dataders/adu_adoration/apartment/option-a-living-east.png

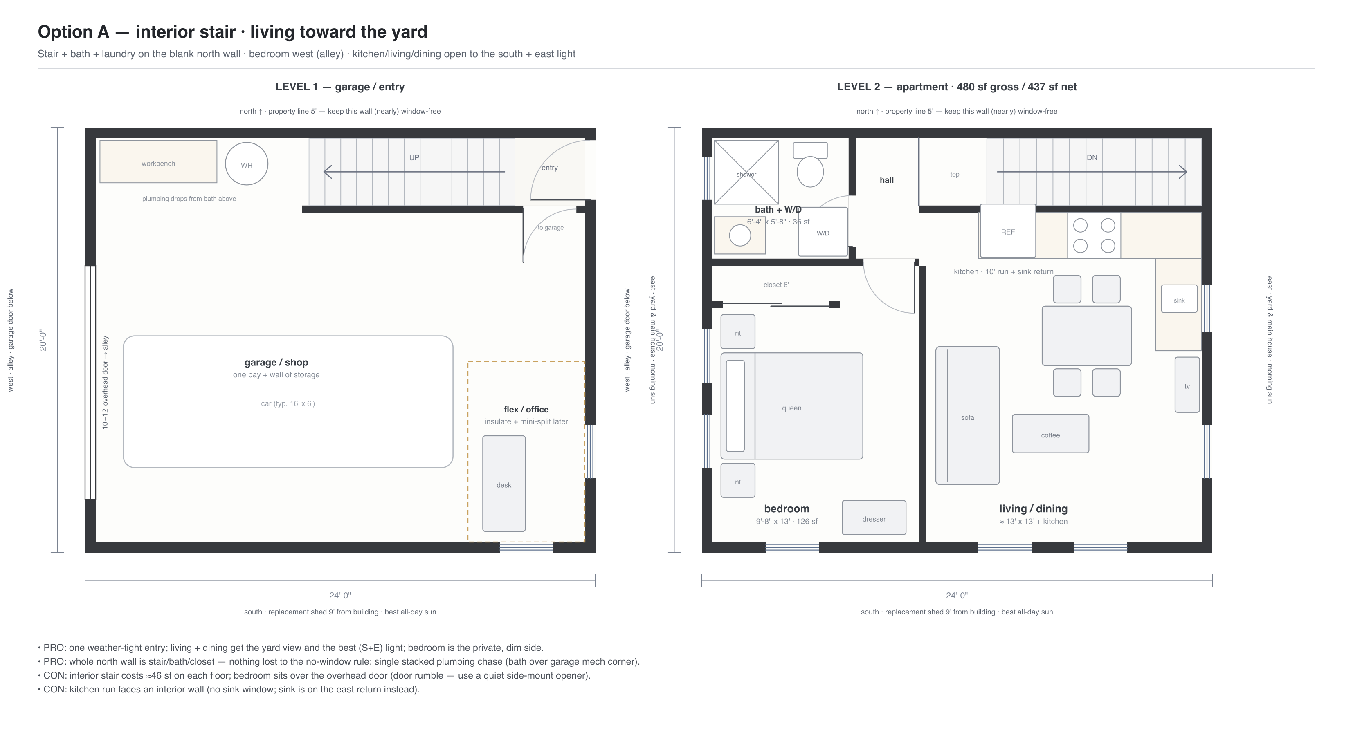
apartment/option-a-living-east.png
