dataders/adu_adoration/apartment/option-b-bedroom-east.png

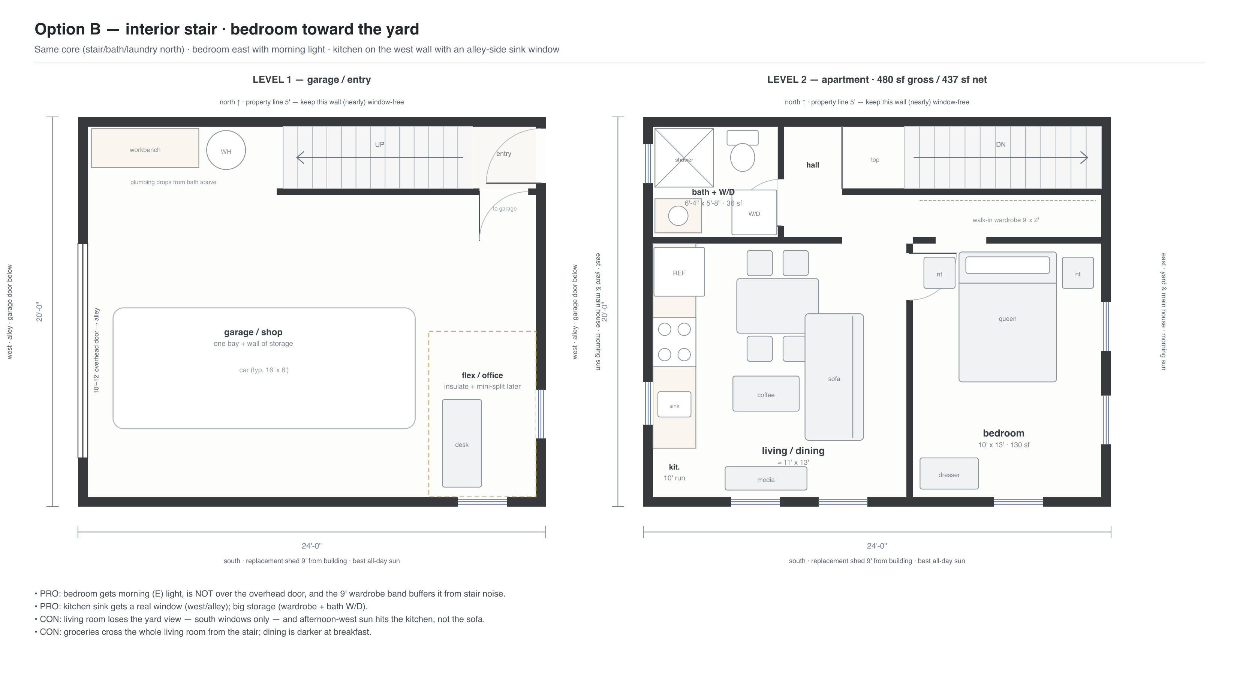
apartment/option-b-bedroom-east.png
