dataders/adu_adoration/apartment/option-c-exterior-stair.png

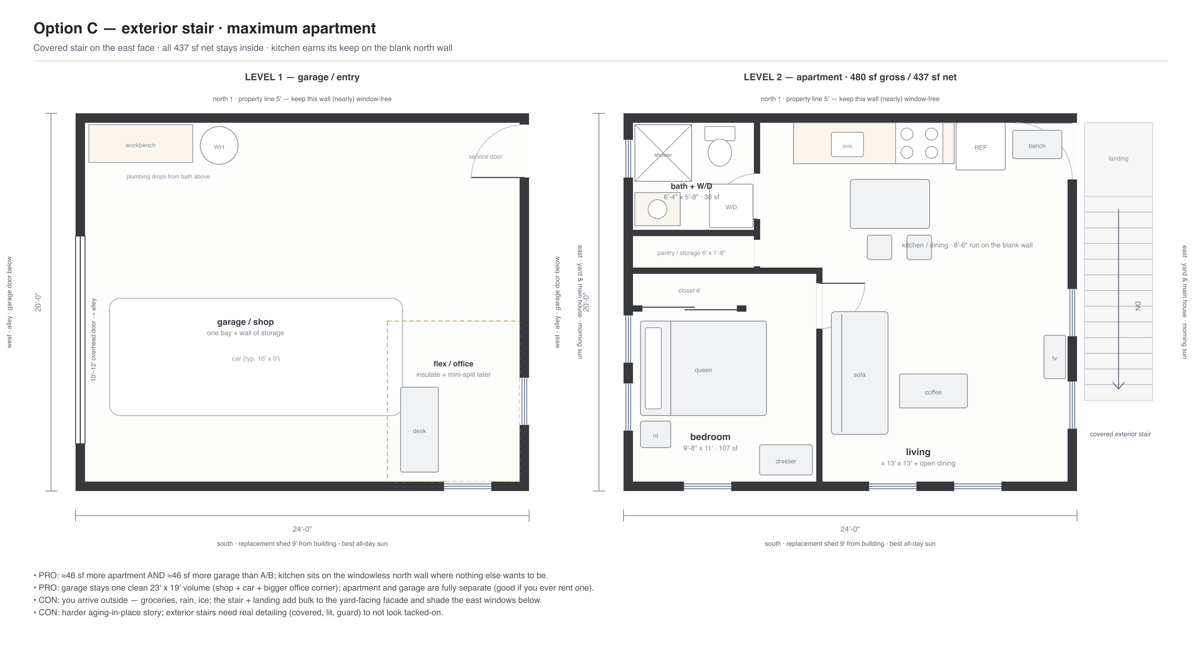
apartment/option-c-exterior-stair.png
