dataders/adu_adoration/apartment/option-d-south-stair-roof-aware.png

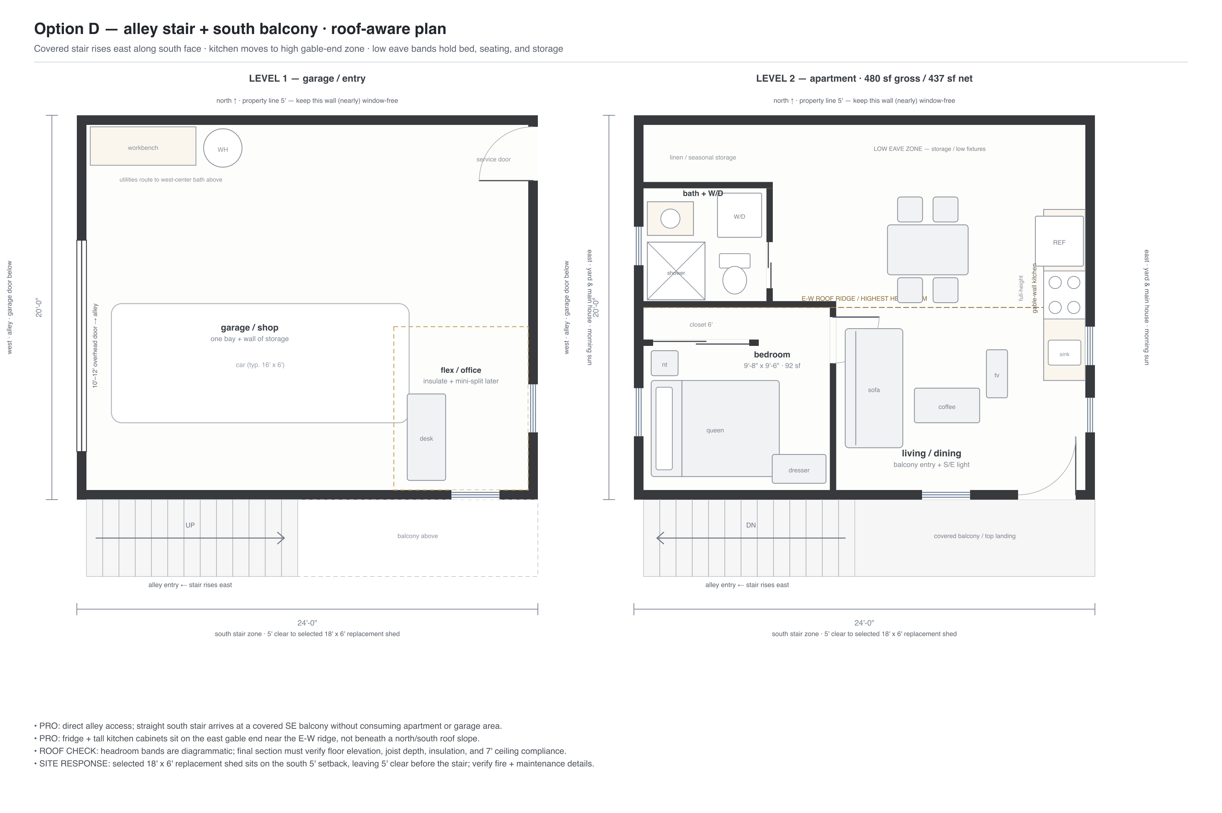
apartment/option-d-south-stair-roof-aware.png
