dataders/adu_adoration/apartment/option-f-alternative-garden.png

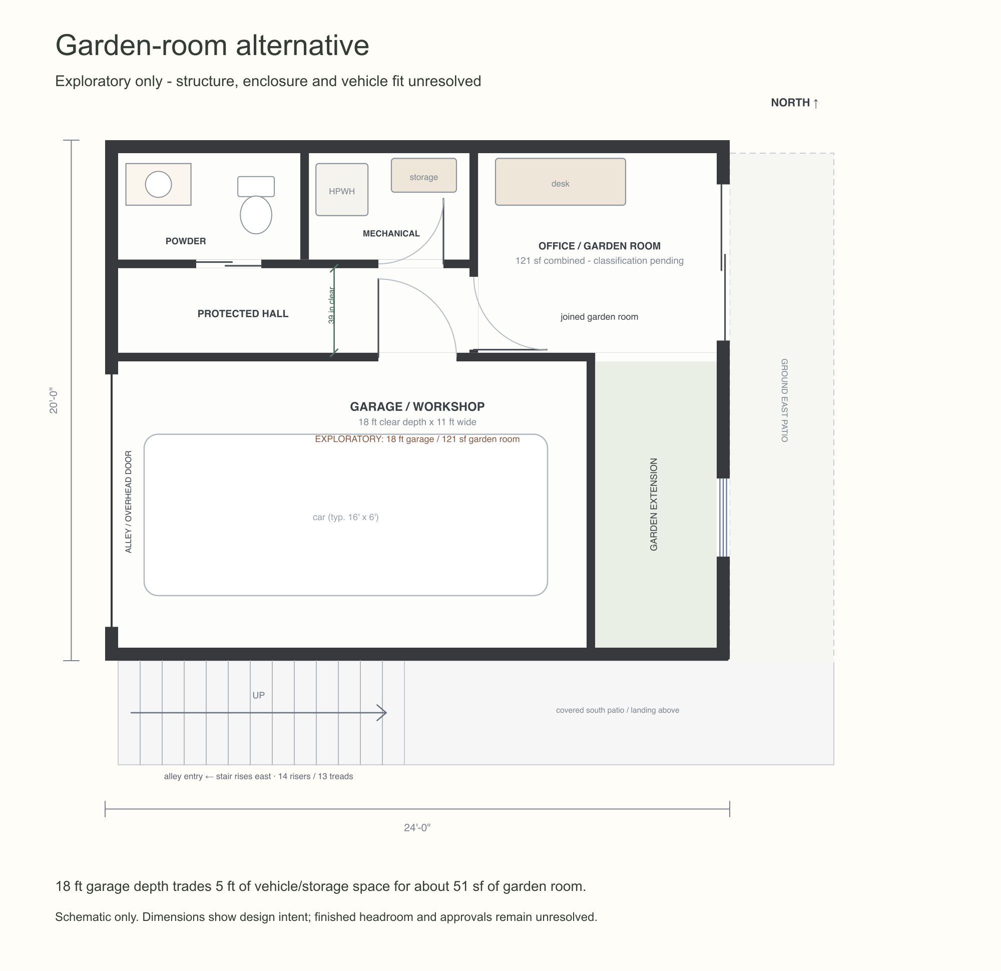
apartment/option-f-alternative-garden.png
