dataders/adu_adoration/apartment/option-f-level-1.png

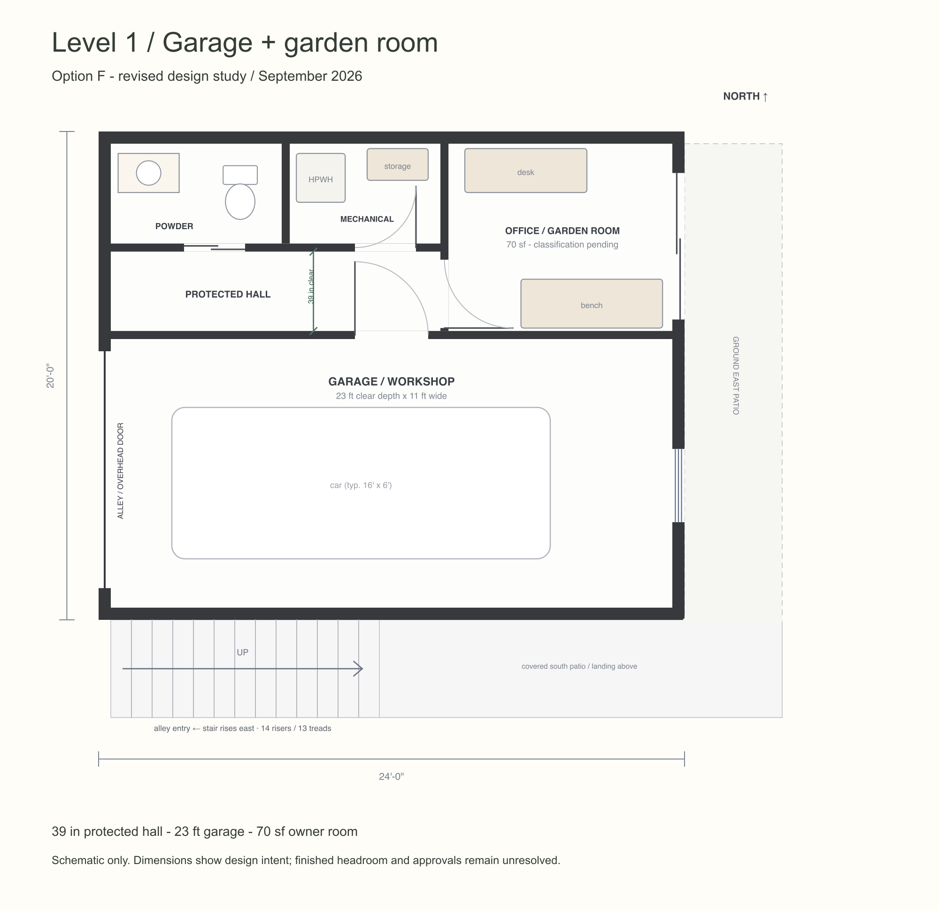
apartment/option-f-level-1.png
