dataders/adu_adoration/apartment/option-f-level-2.png

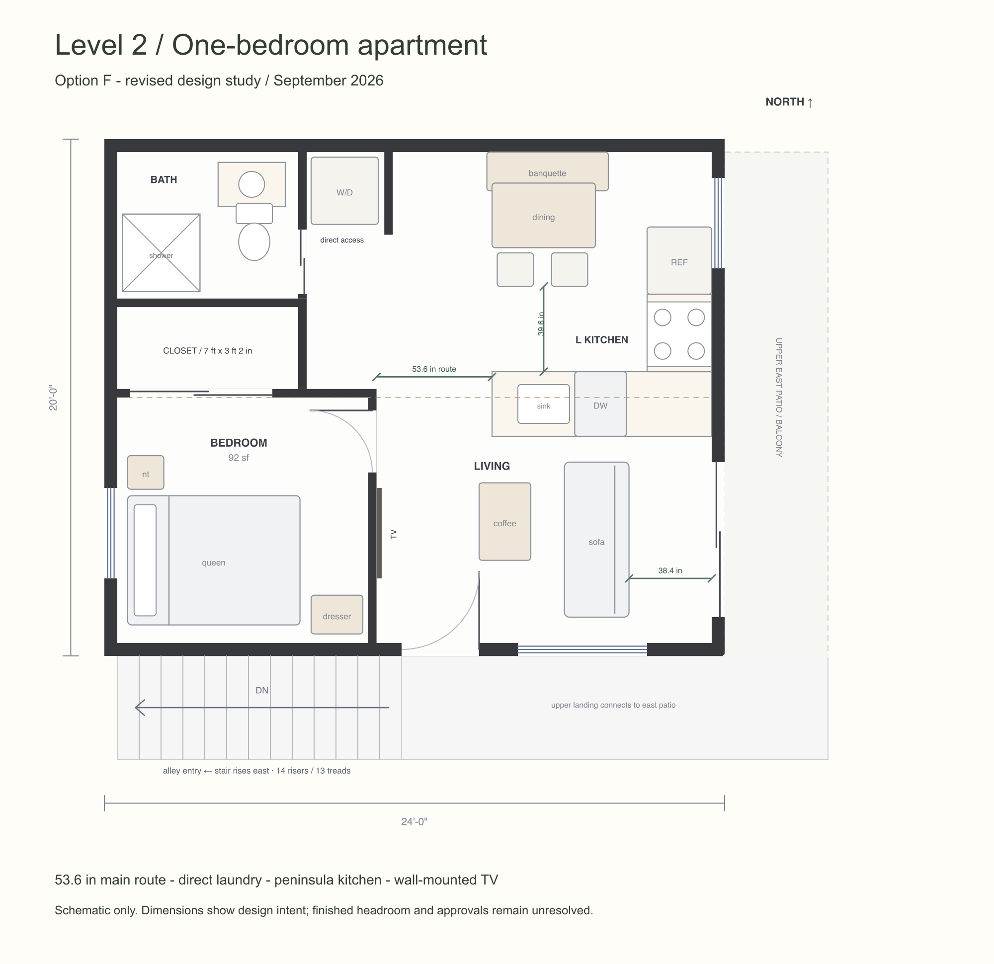
apartment/option-f-level-2.png
