dataders/adu_adoration/apartment/option-f-recommended-development.png

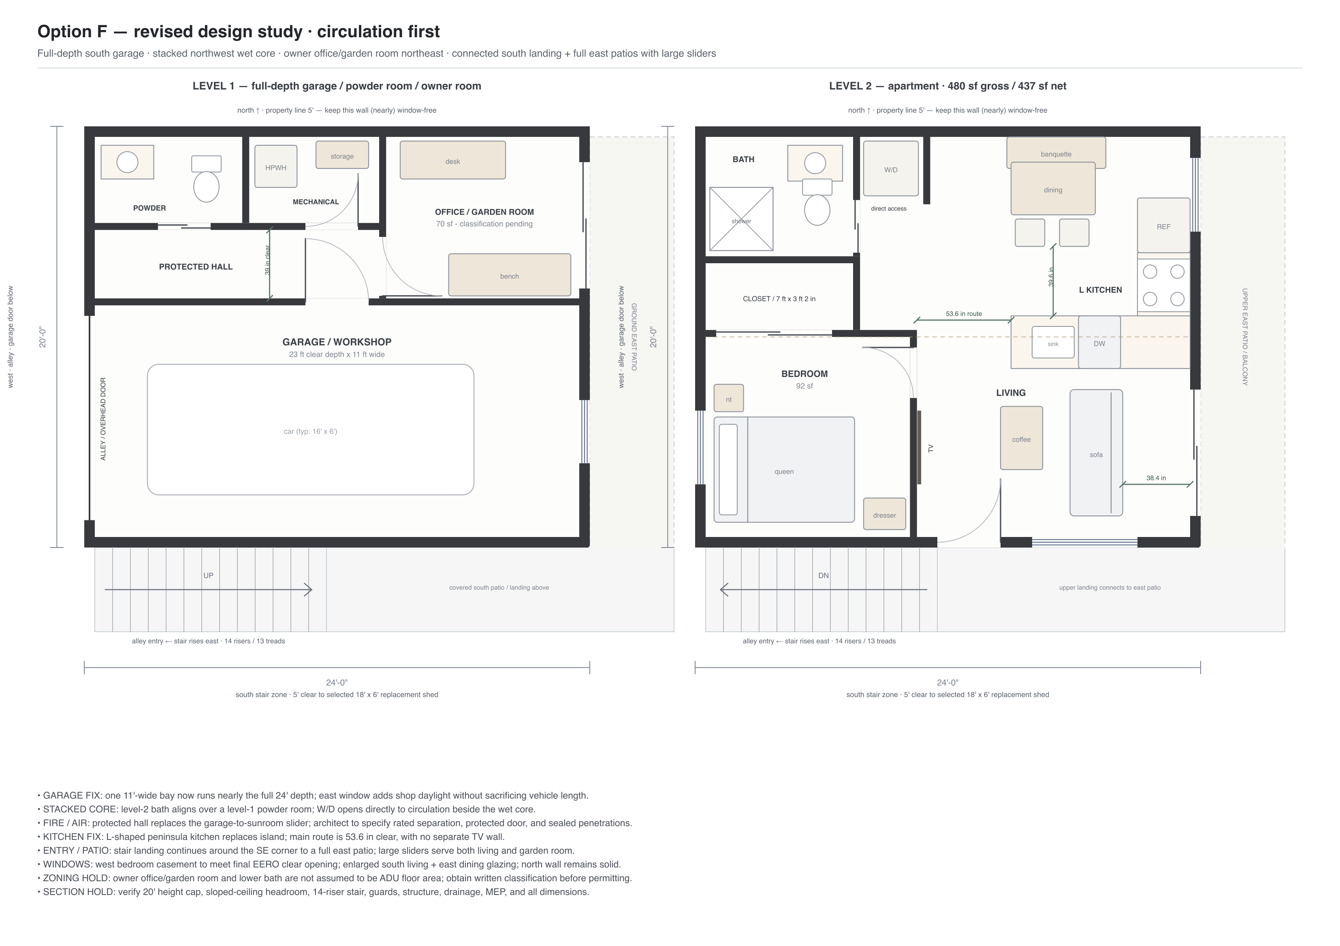
apartment/option-f-recommended-development.png
