dataders/adu_adoration/images/06-satellite-parcel-outline.png

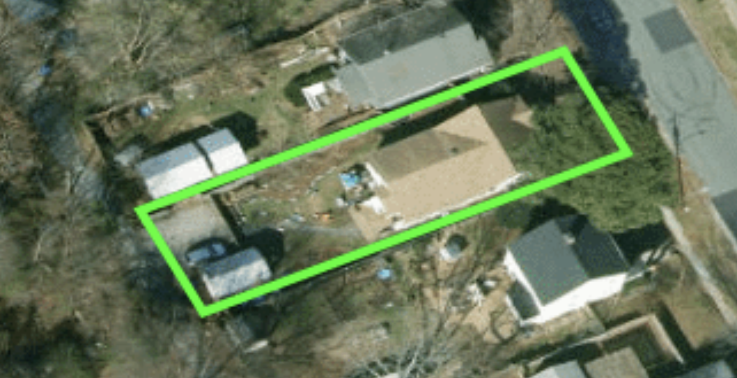
images/06-satellite-parcel-outline.png
