dataders/adu_adoration/images/07-satellite-oblique-3d.png

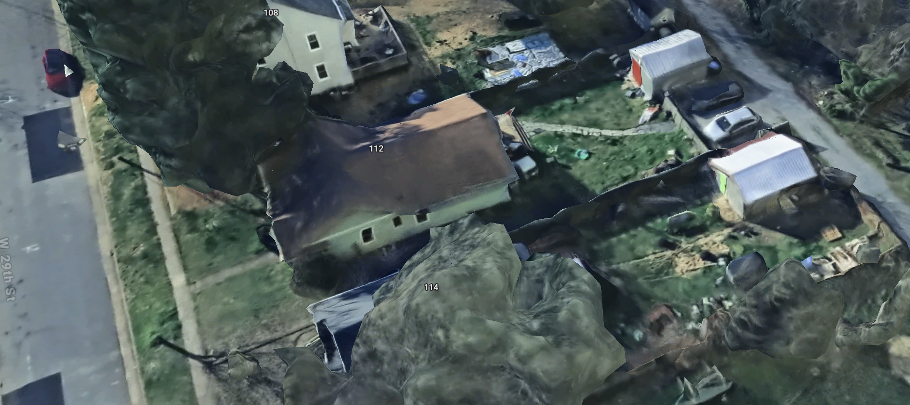
images/07-satellite-oblique-3d.png
