dataders/adu_adoration/images/09-backyard-shed-facing-west.jpg

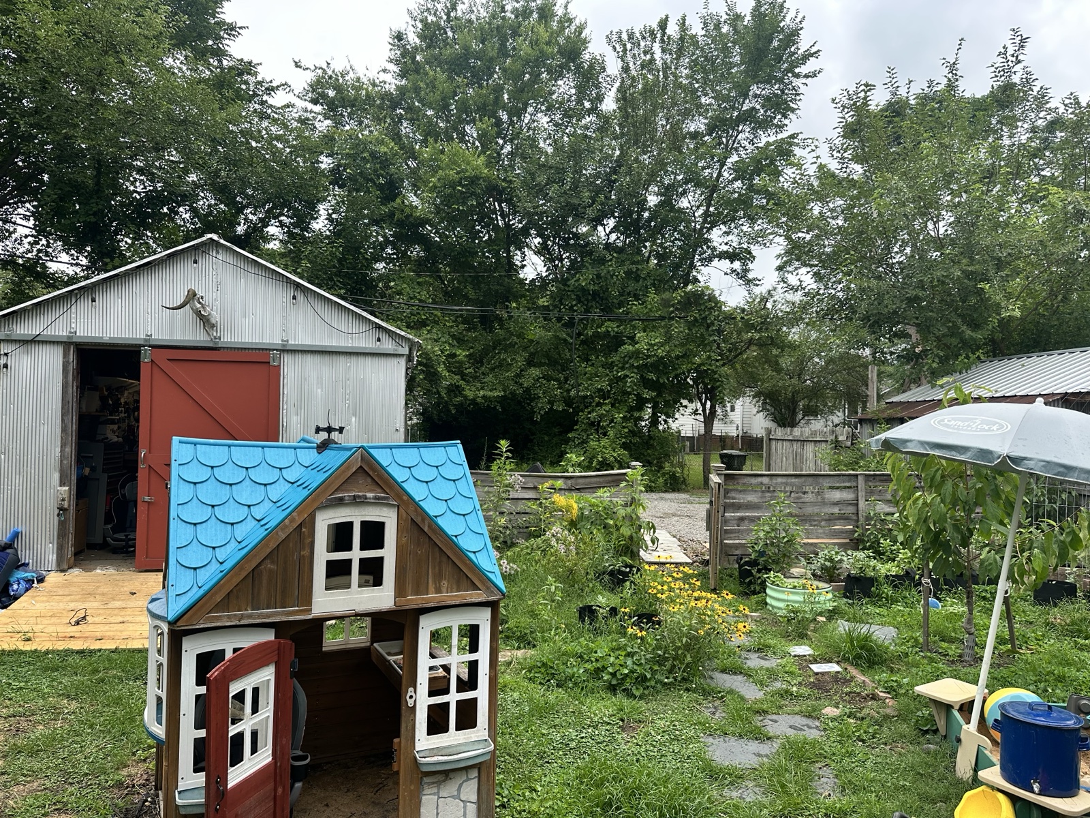
images/09-backyard-shed-facing-west.jpg
