dataders/adu_adoration/images/11-backyard-alley-parking-facing-east.jpg

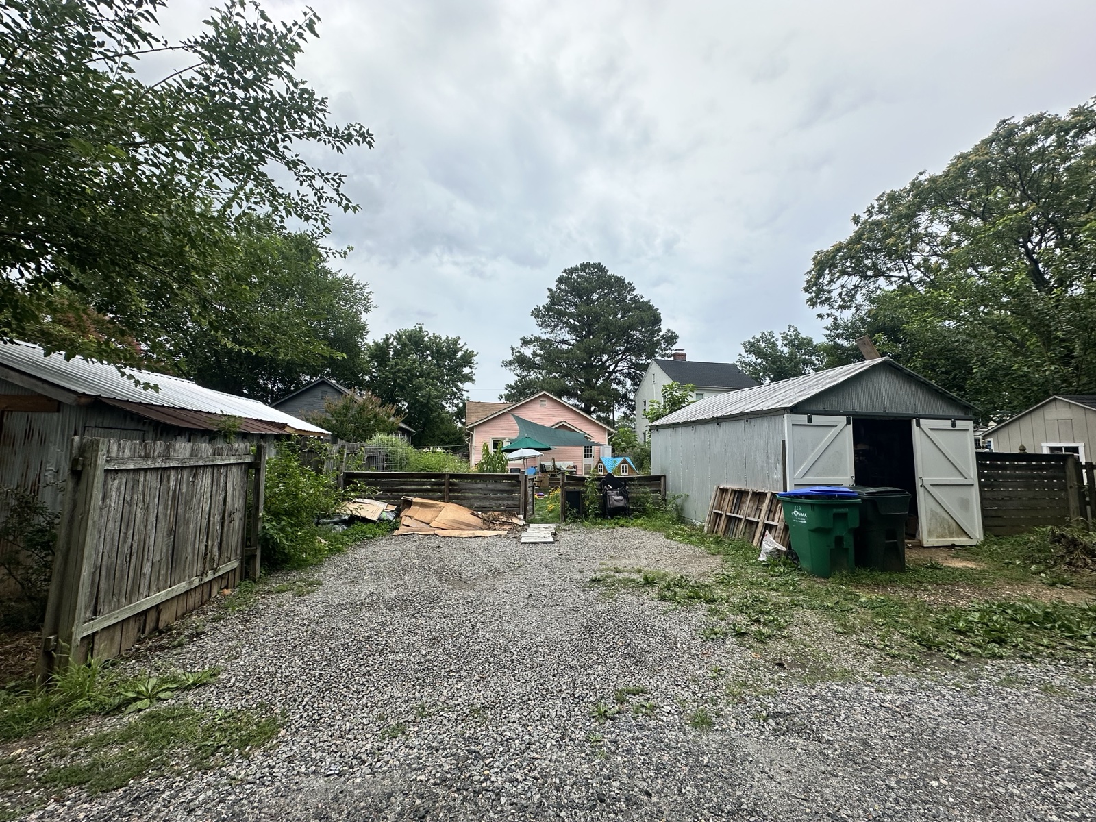
images/11-backyard-alley-parking-facing-east.jpg
