dataders/adu_adoration/inspiration/01-gold-siding-black-windows-bay-tower.jpg

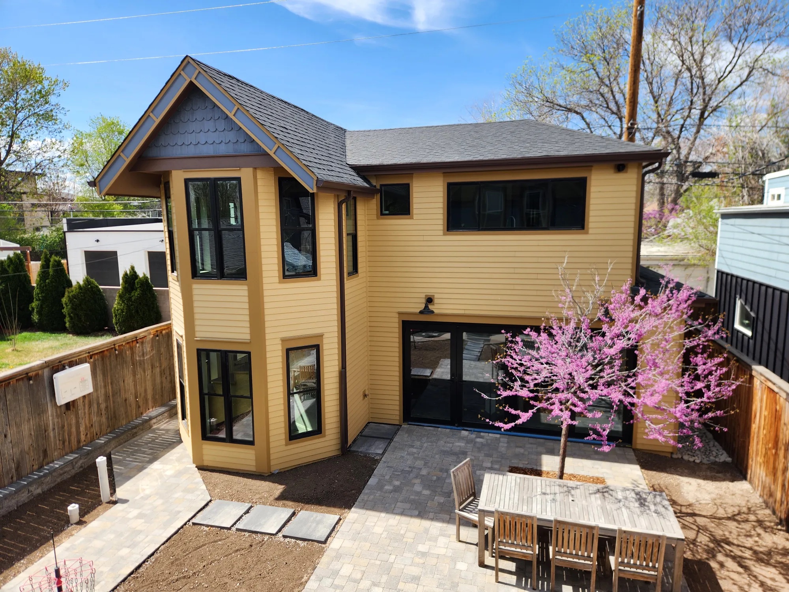
inspiration/01-gold-siding-black-windows-bay-tower.jpg
