dataders/adu_adoration/inspiration/02-modern-taupe-shed-roof-awning-windows.jpg

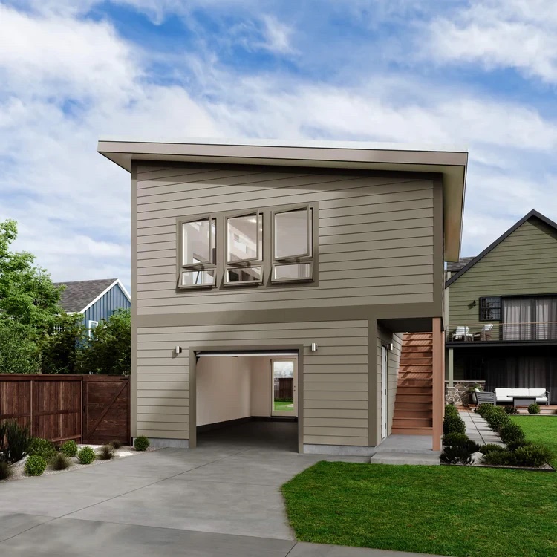
inspiration/02-modern-taupe-shed-roof-awning-windows.jpg
