dataders/adu_adoration/inspiration/03-craftsman-gray-red-trim-carriage-door.jpg

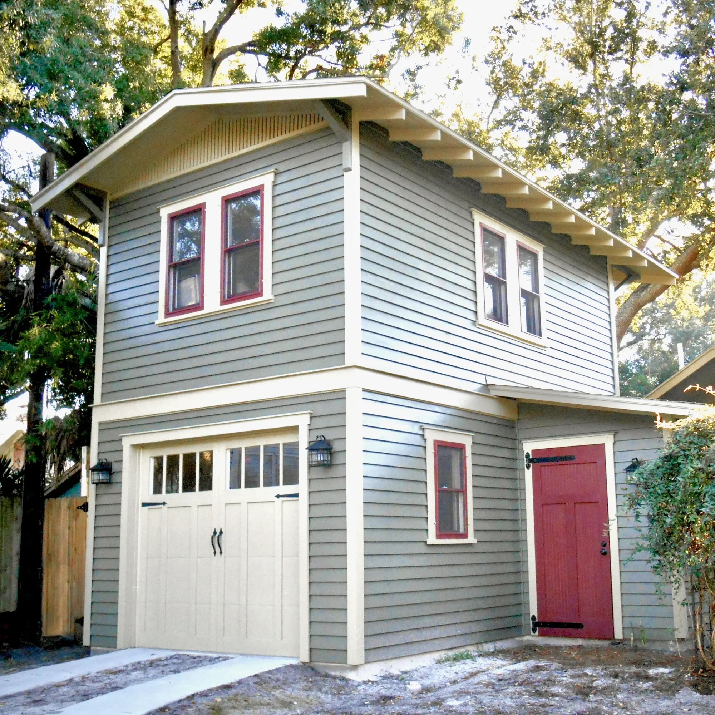
inspiration/03-craftsman-gray-red-trim-carriage-door.jpg
