dataders/adu_adoration/inspiration/04-olive-carriage-door-balcony-cottage.jpg

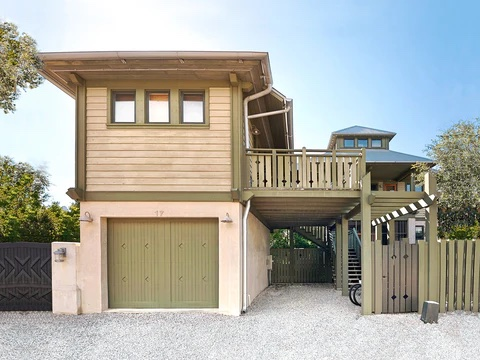
inspiration/04-olive-carriage-door-balcony-cottage.jpg
