dataders/adu_adoration/inspiration/05-brick-shed-roof-black-windows-wood-door.jpg

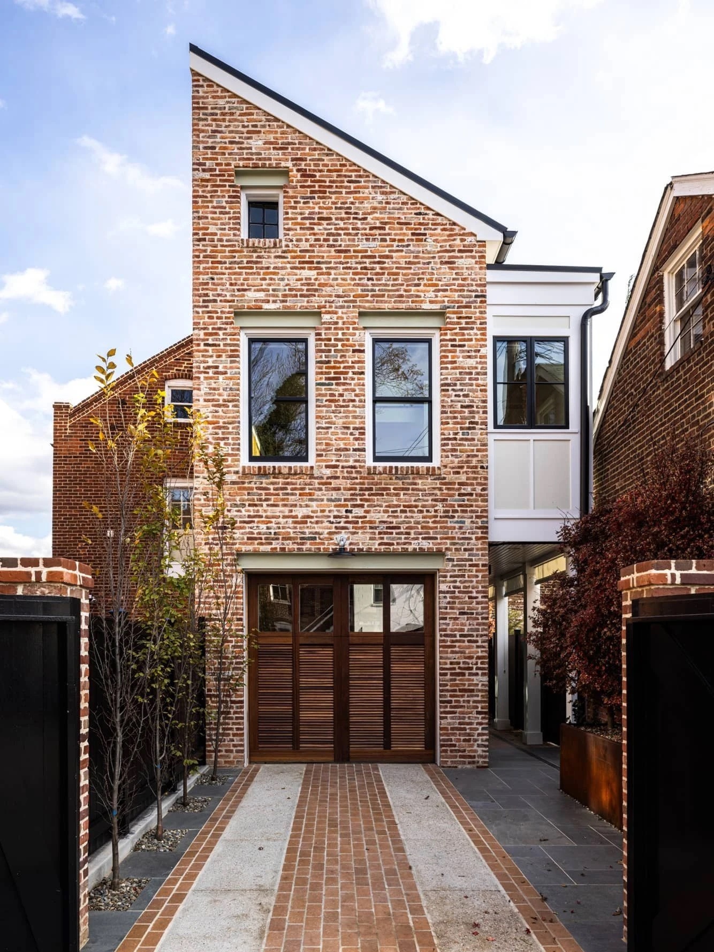
inspiration/05-brick-shed-roof-black-windows-wood-door.jpg
