dataders/adu_adoration/inspiration/06-modern-olive-bronze-windows-corner-glass.jpg

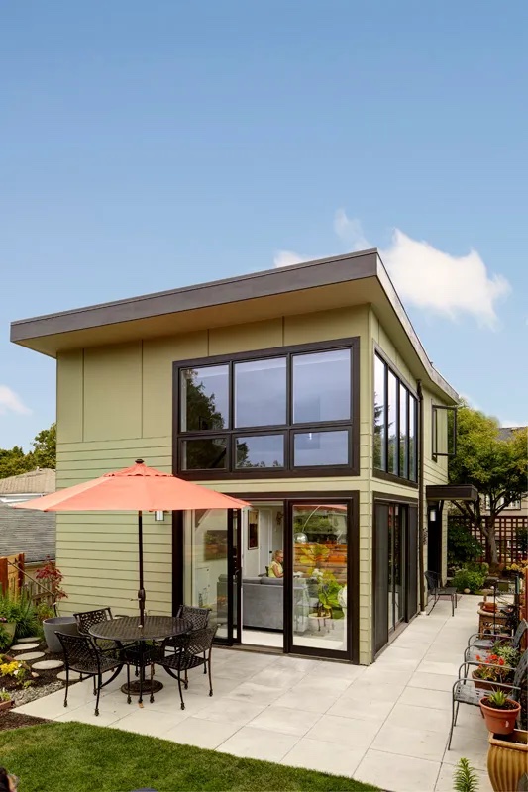
inspiration/06-modern-olive-bronze-windows-corner-glass.jpg
