dataders/adu_adoration/inspiration/pin-407012885098091217-pin.jpg

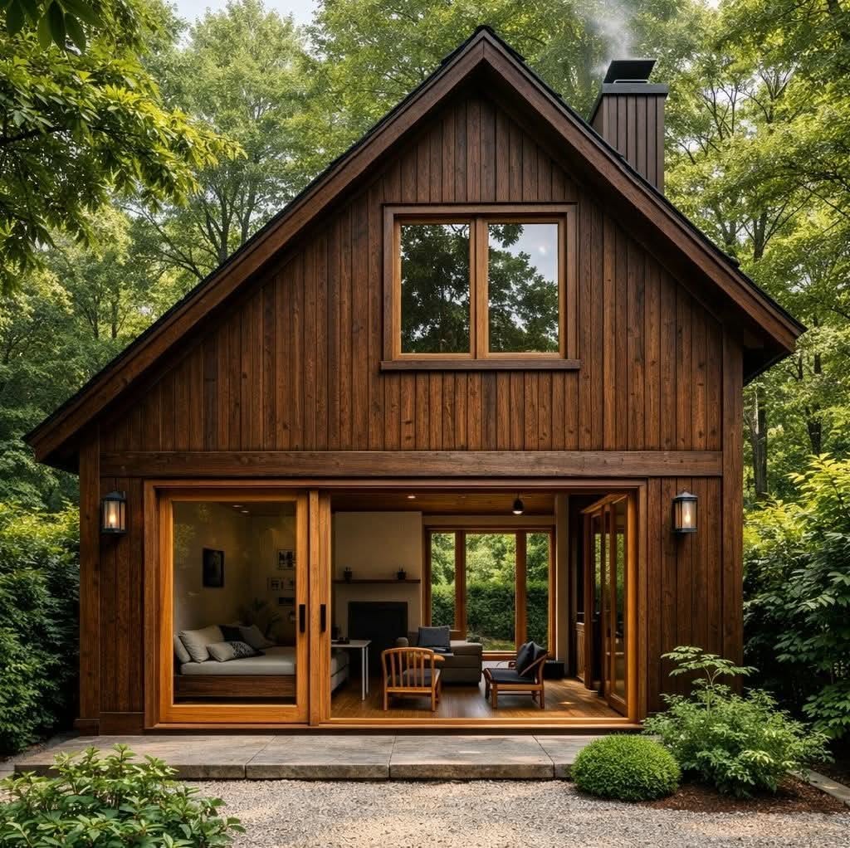
inspiration/pin-407012885098091217-pin.jpg
