dataders/adu_adoration/inspiration/pin-407012885098092414-62k-views-1-4k-reactions-a-small-cabin-a-big-for.jpg

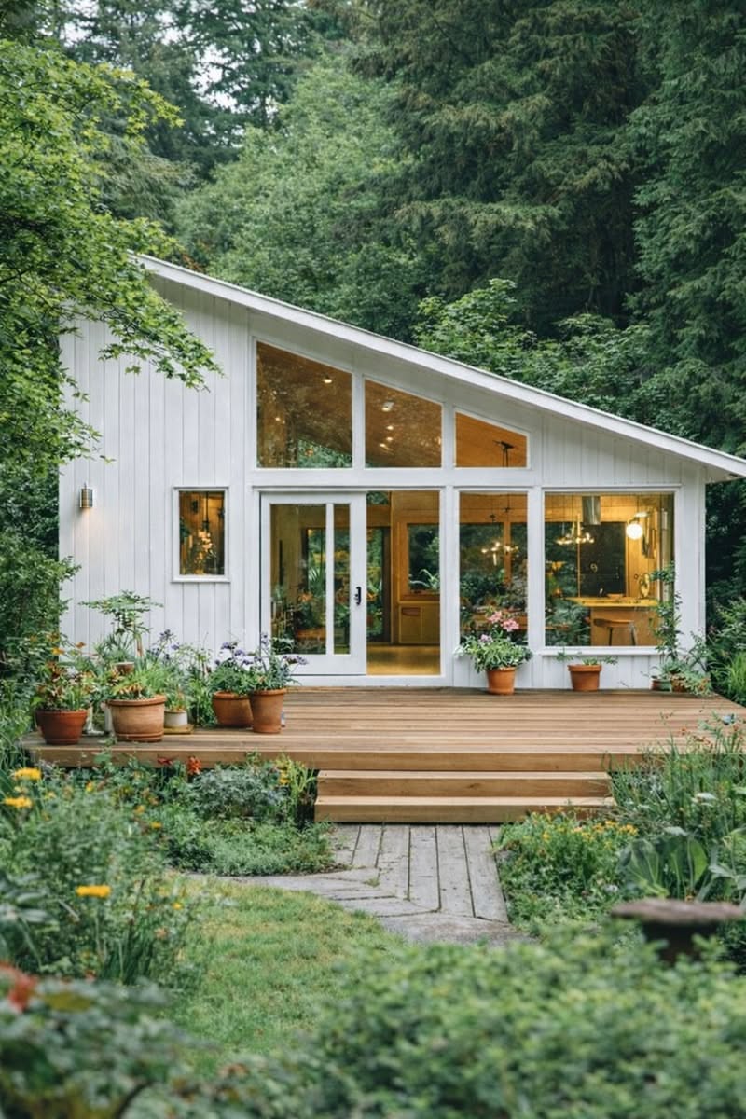
inspiration/pin-407012885098092414-62k-views-1-4k-reactions-a-small-cabin-a-big-for.jpg
