dataders/adu_adoration/inspiration/pin-407012885098092424-green-craftsman-shed-with-wooden-doors-and-bear.jpg

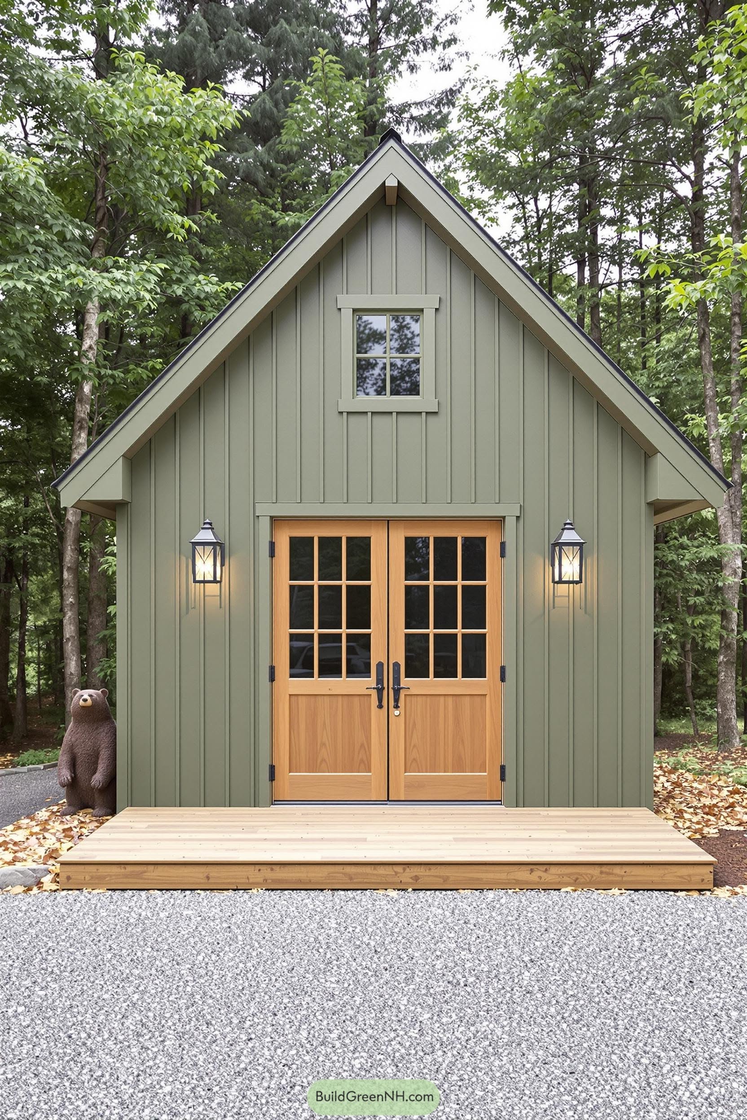
inspiration/pin-407012885098092424-green-craftsman-shed-with-wooden-doors-and-bear.jpg
