dataders/adu_adoration/inspiration/pin-407012885098092436-the-apartment-above-the-garage-received-a-dormer.jpg

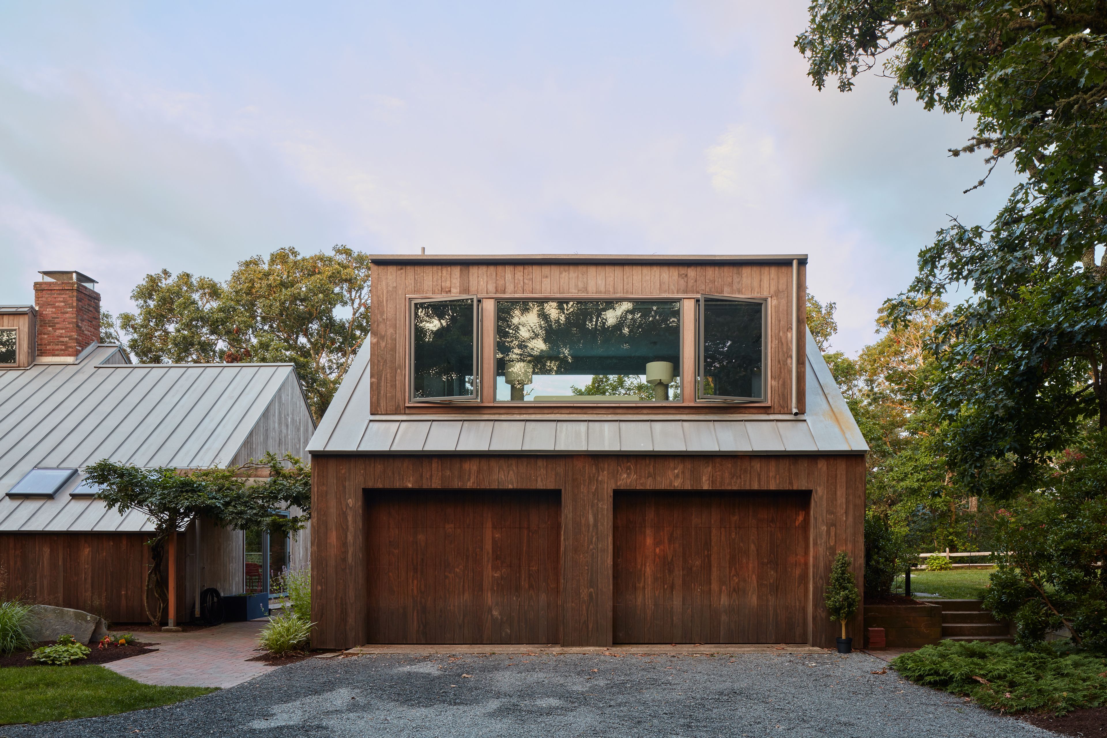
inspiration/pin-407012885098092436-the-apartment-above-the-garage-received-a-dormer.jpg
