dataders/adu_adoration/inspiration/pin-407012885098092439-a-brunswick-home-re-beautified-decor-maine.jpg

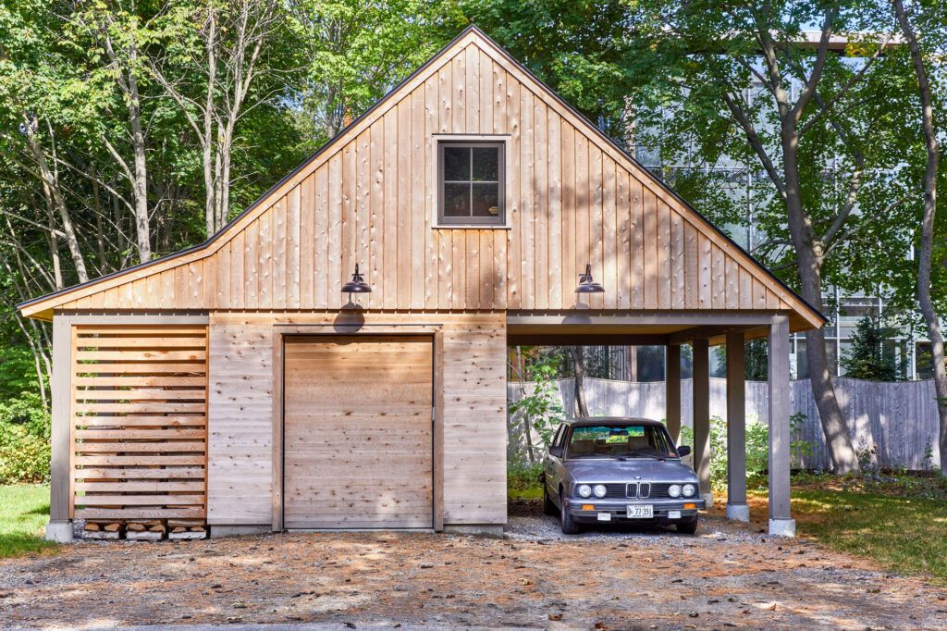
inspiration/pin-407012885098092439-a-brunswick-home-re-beautified-decor-maine.jpg
