dataders/adu_adoration/inspiration/pin-407012885098092445-pin.jpg

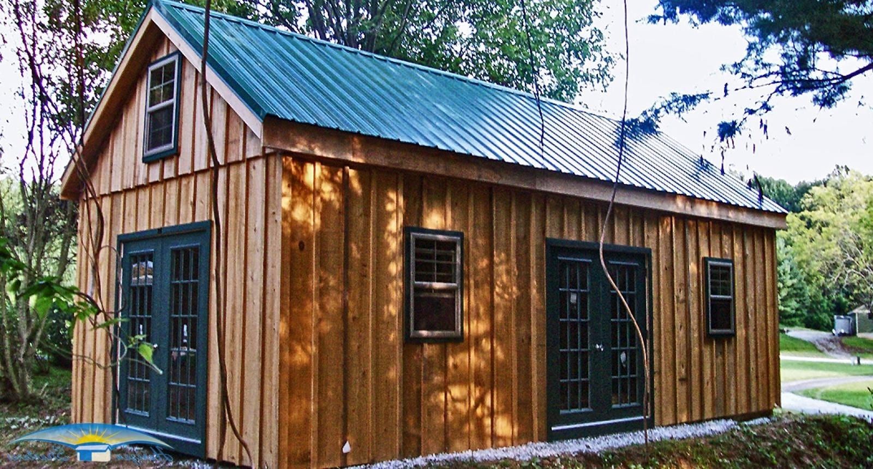
inspiration/pin-407012885098092445-pin.jpg
