dataders/adu_adoration/inspiration/pin-407012885098092450-pin.jpg

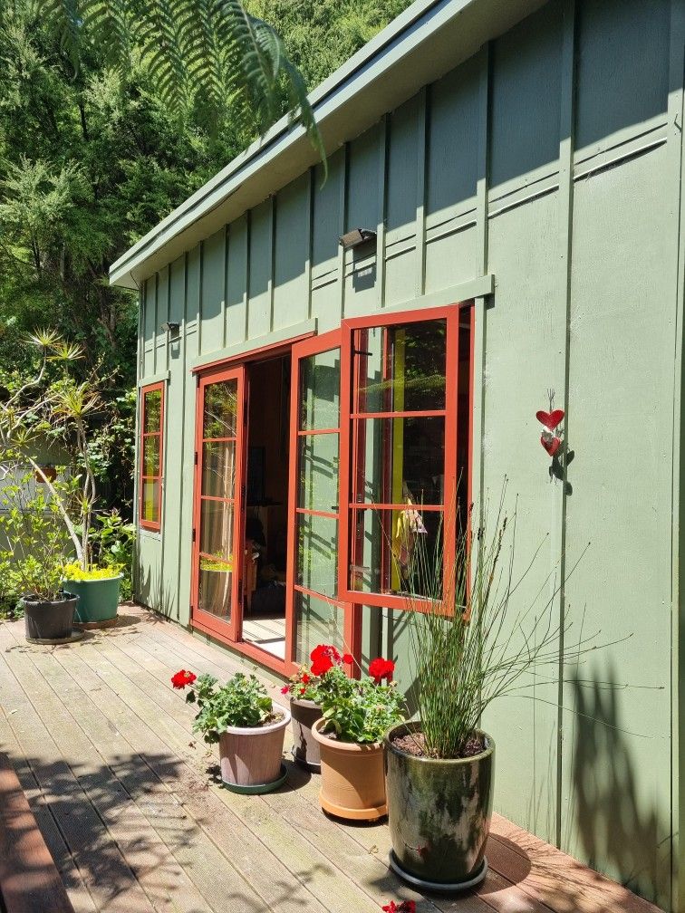
inspiration/pin-407012885098092450-pin.jpg
