dataders/adu_adoration/inspiration/pin-407012885098092619-experience-the-meticulous-craftsmanship-of-our-c.jpg

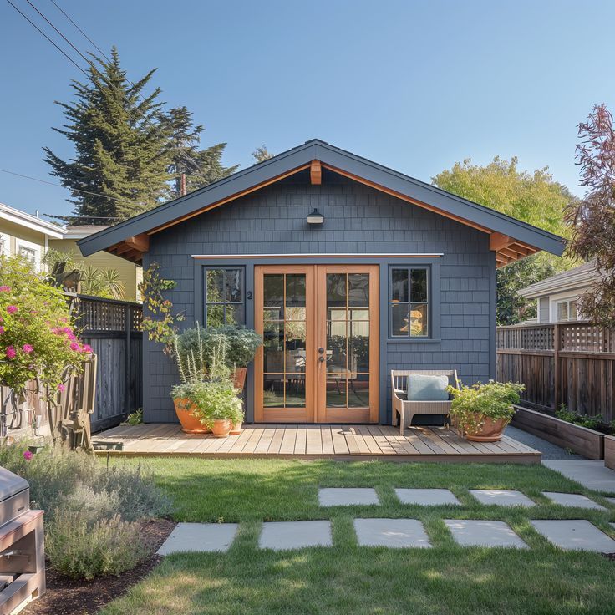
inspiration/pin-407012885098092619-experience-the-meticulous-craftsmanship-of-our-c.jpg
