dataders/adu_adoration/inspiration/pin-407012885098092621-rent-out-your-large-family-home-and-live-in-an-a.jpg

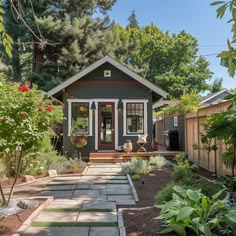
inspiration/pin-407012885098092621-rent-out-your-large-family-home-and-live-in-an-a.jpg
