dataders/adu_adoration/inspiration/pin-407012885098092629-15.jpg

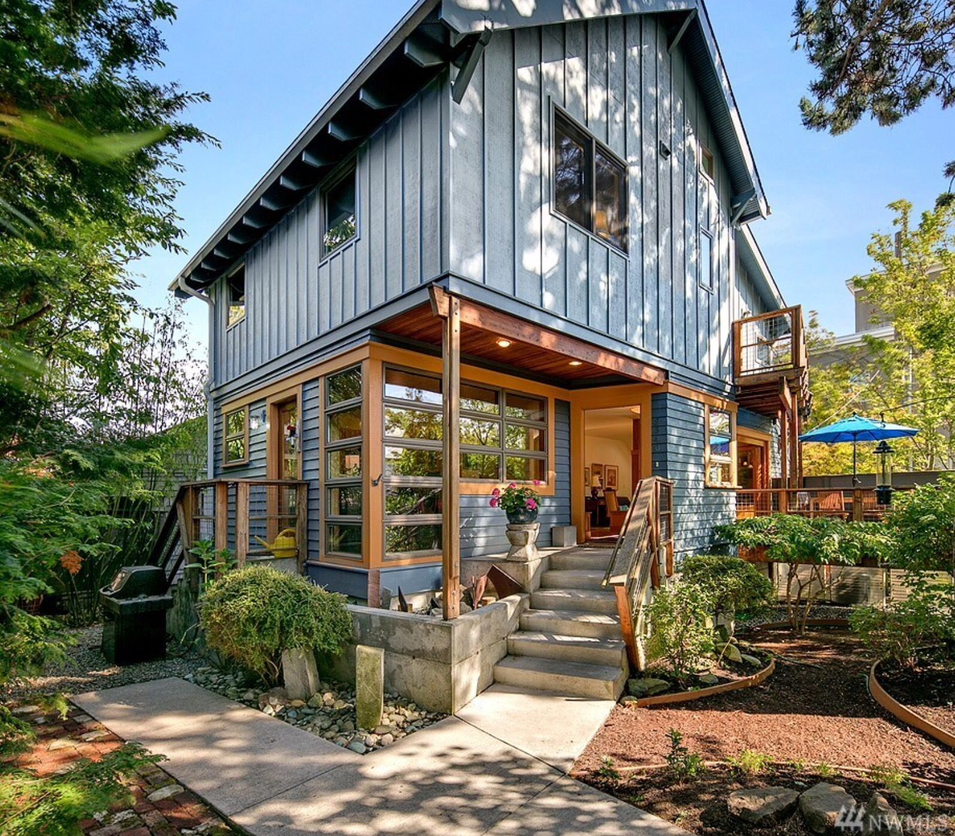
inspiration/pin-407012885098092629-15.jpg
