dataders/adu_adoration/inspiration/pin-407012885098092632-garden-garage-apartment-with-glass-corner-sunroo.jpg

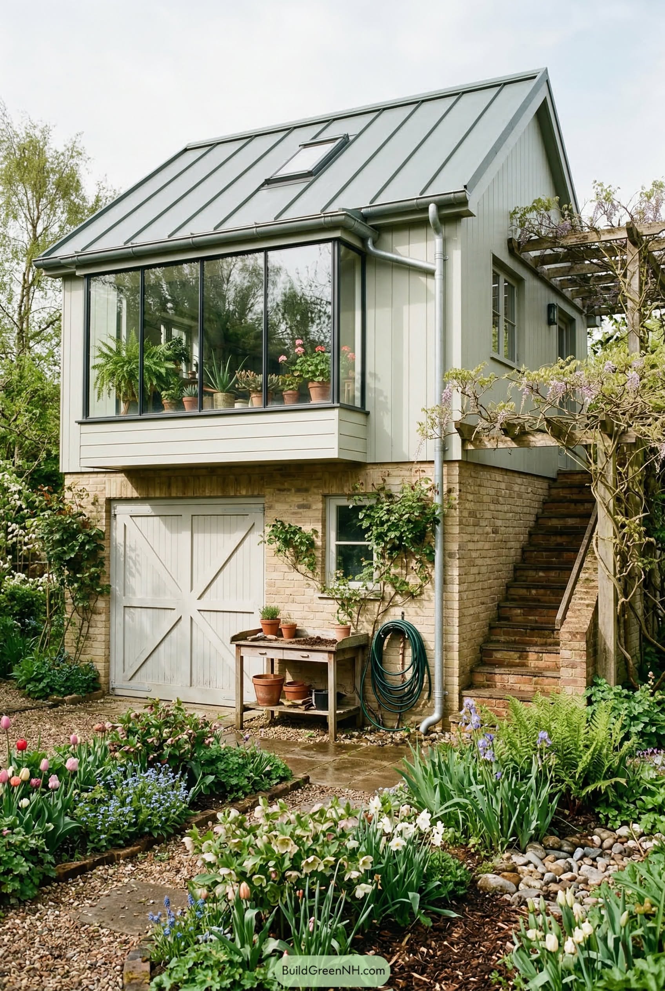
inspiration/pin-407012885098092632-garden-garage-apartment-with-glass-corner-sunroo.jpg
