dataders/adu_adoration/inspiration/pin-407012885098092633-blue-gray-two-story-garage-apartment-in-lush-gar.jpg

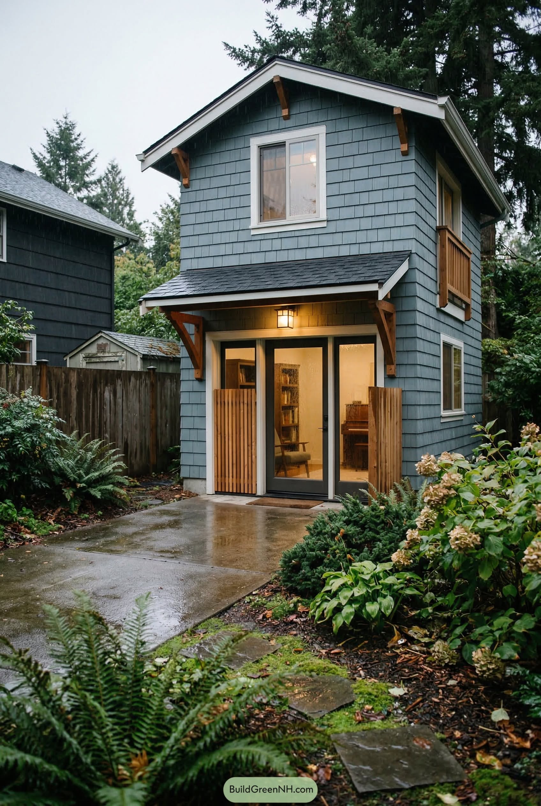
inspiration/pin-407012885098092633-blue-gray-two-story-garage-apartment-in-lush-gar.jpg
