dataders/adu_adoration/inspiration/pin-407012885098095681-pin.jpg

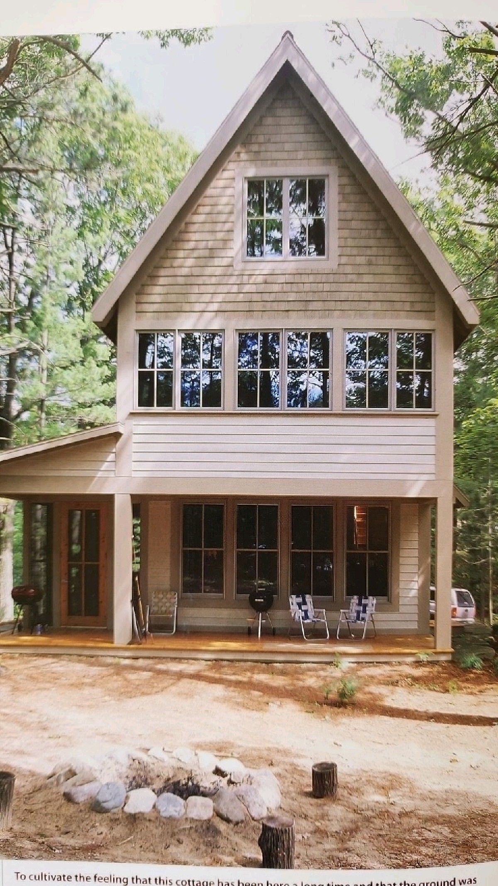
inspiration/pin-407012885098095681-pin.jpg
