dataders/adu_adoration/inspiration/pin-407012885098095682-pin.jpg

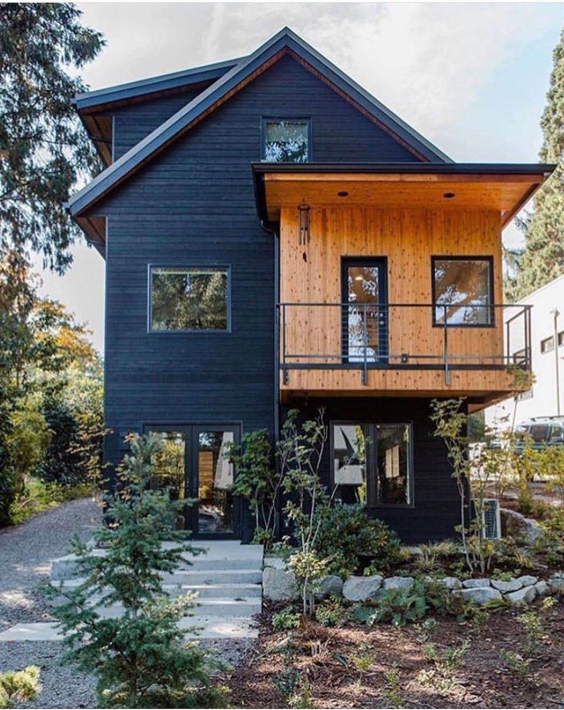
inspiration/pin-407012885098095682-pin.jpg
