dataders/adu_adoration/model/adu-option-e-axon.png

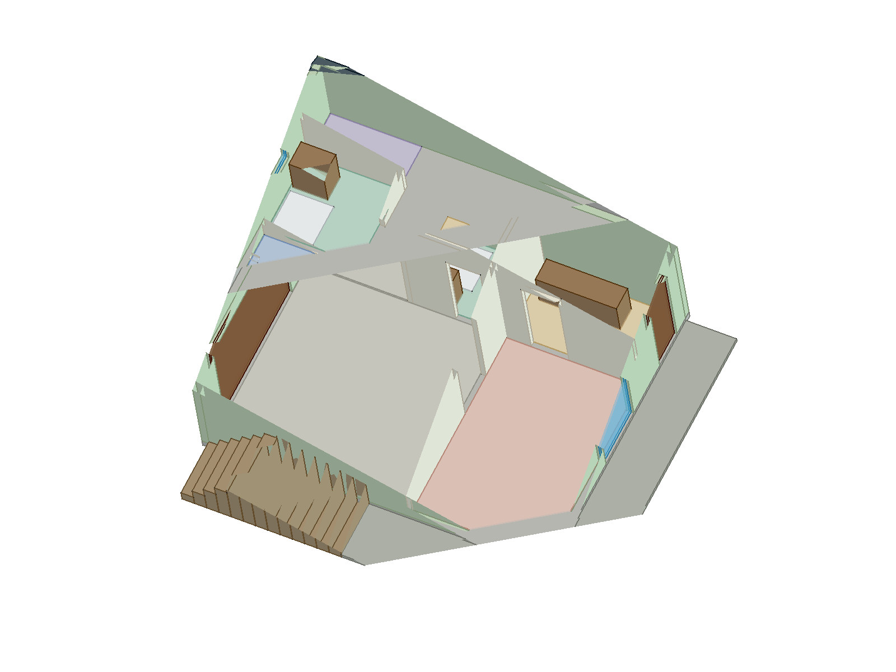
model/adu-option-e-axon.png
