dataders/adu_adoration/model/adu-option-e-level-1.png

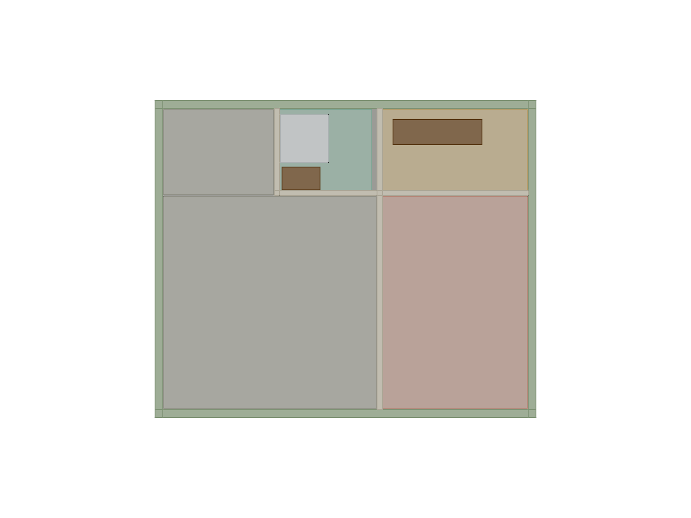
model/adu-option-e-level-1.png
