dataders/adu_adoration/model/adu-option-e-level-2.png

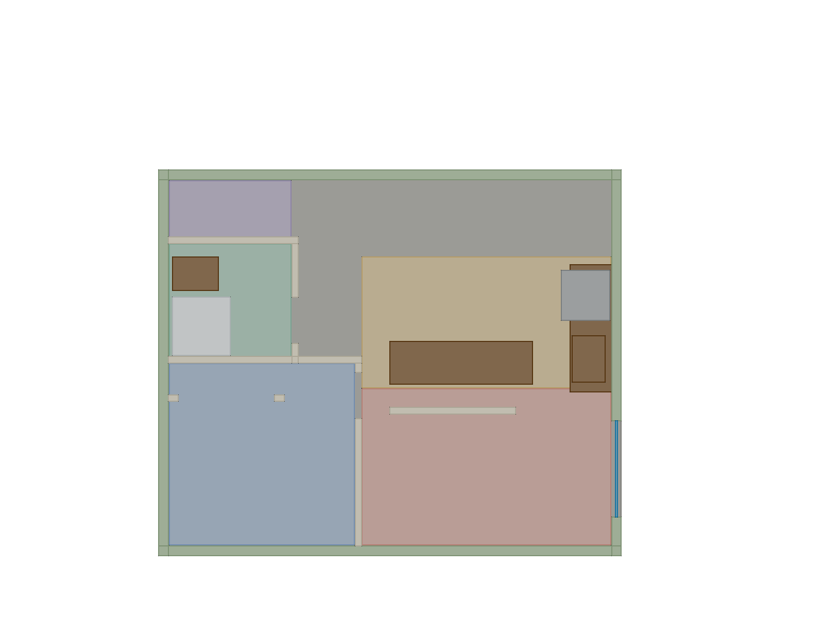
model/adu-option-e-level-2.png
