dataders/adu_adoration/plan/floor-plans-balcony-scheme.png

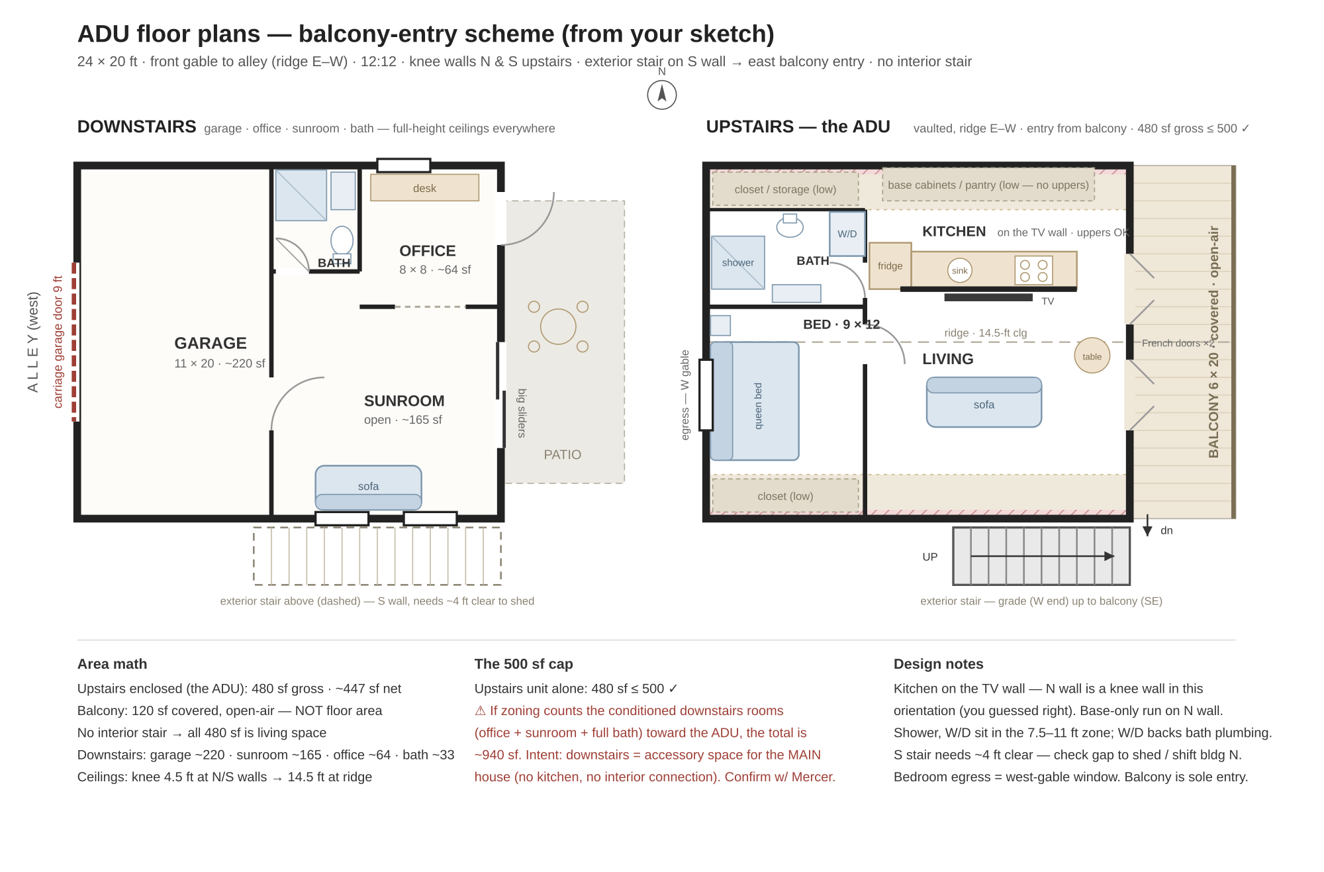
plan/floor-plans-balcony-scheme.png
