dataders/adu_adoration/plan/site-plan.png

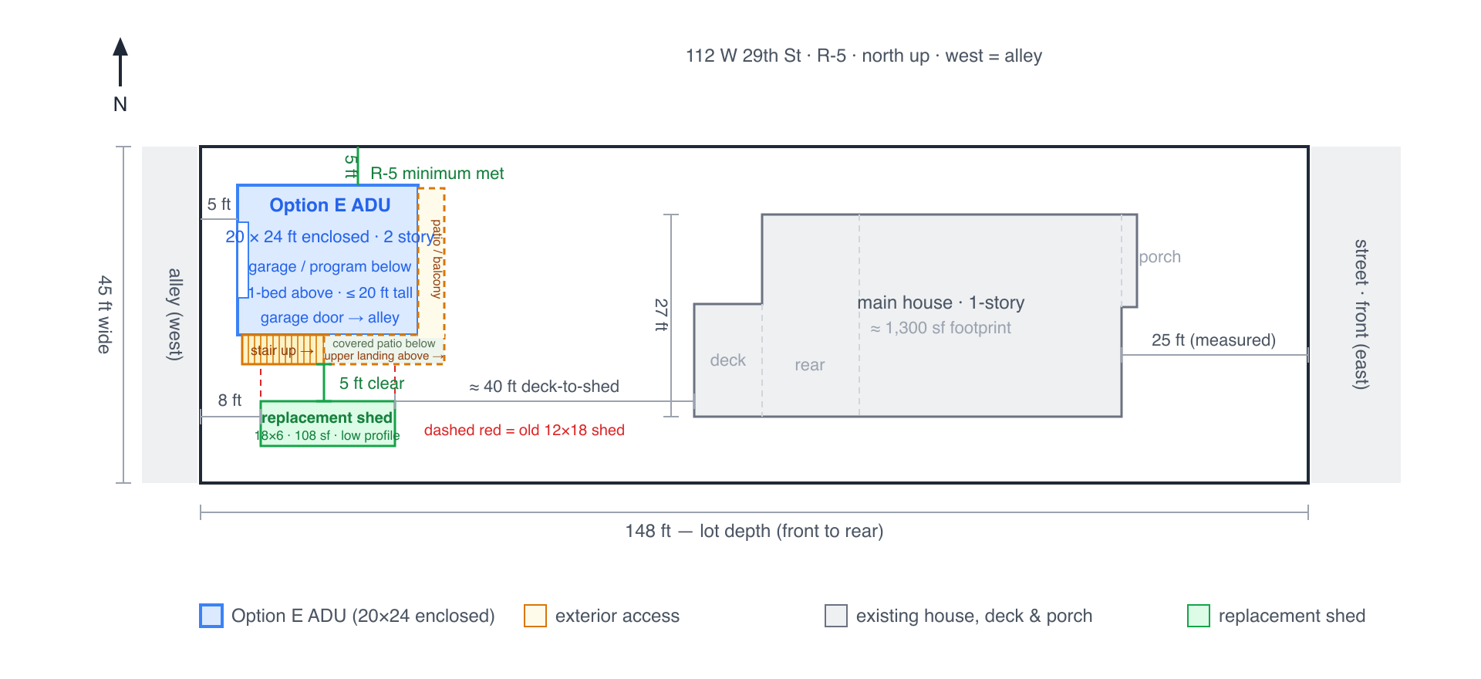
plan/site-plan.png
