dataders/adu_adoration/renderings/alley-massing-incontext.png

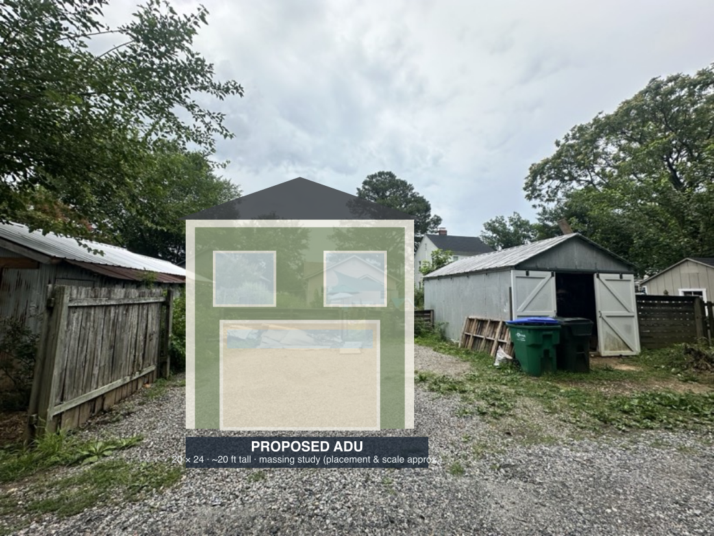
renderings/alley-massing-incontext.png
