dataders/adu_adoration/renderings/alley-view-craftsman.png

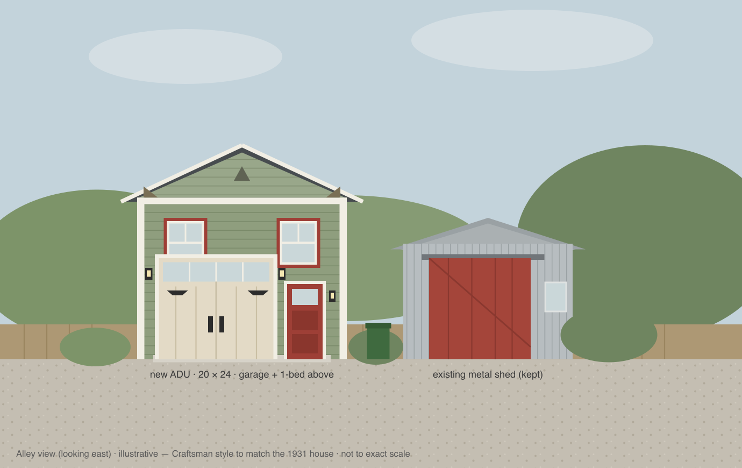
renderings/alley-view-craftsman.png
