dataders/adu_adoration/renderings/layout-c-alley-photoreal.png

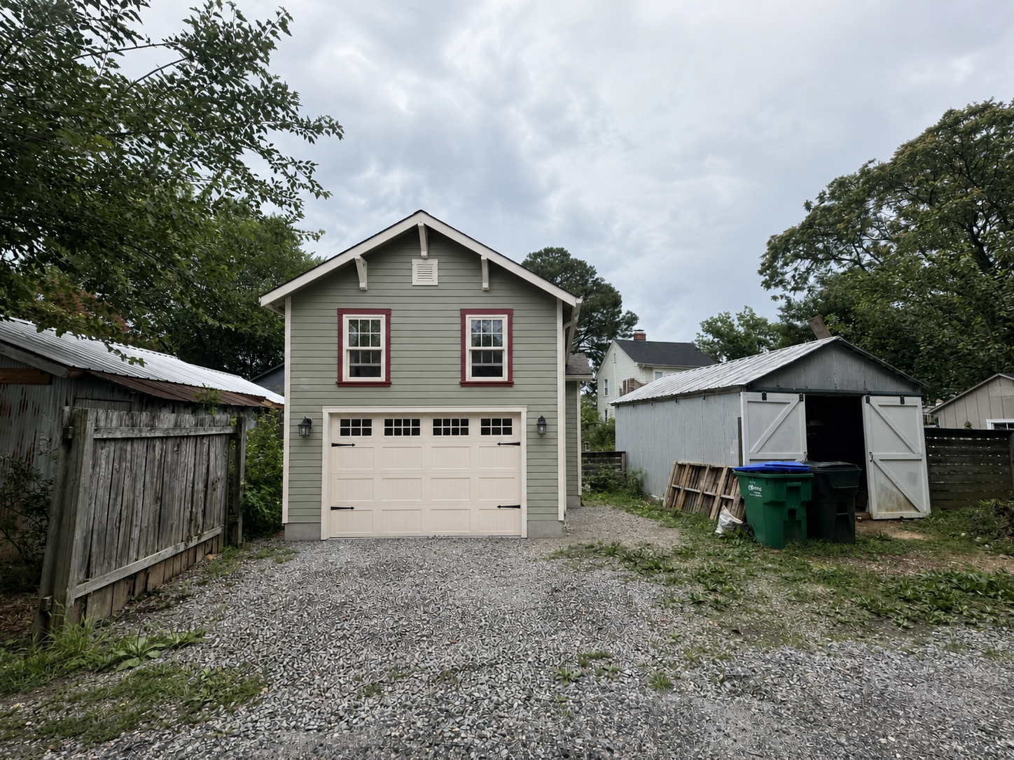
renderings/layout-c-alley-photoreal.png
