dataders/adu_adoration/renderings/layout-c-yard-photoreal.png

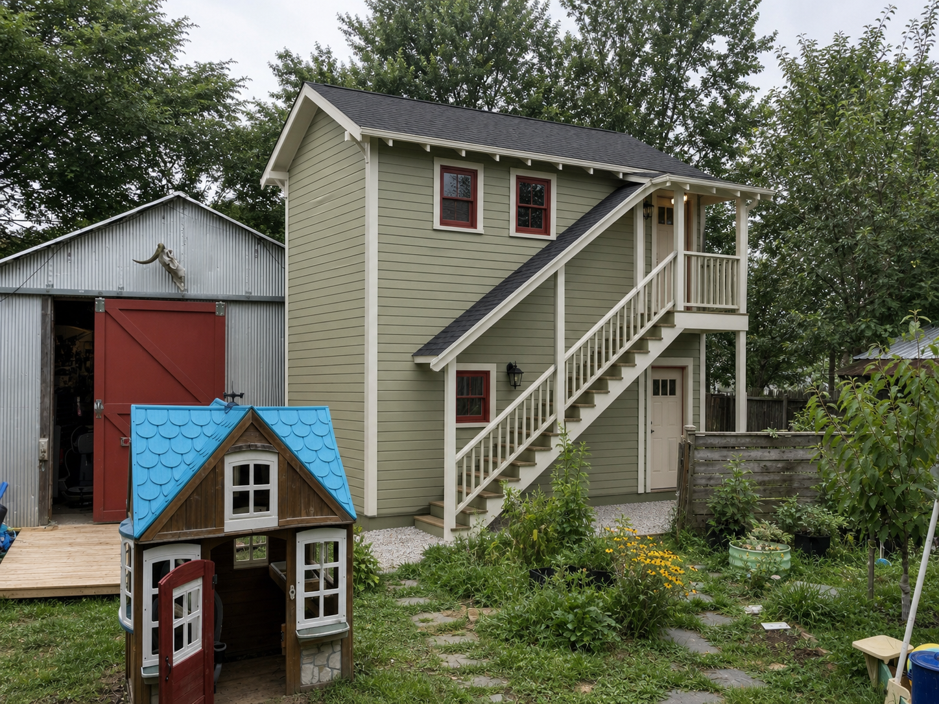
renderings/layout-c-yard-photoreal.png
