dataders/adu_adoration/renderings/massing-3d-alley-view.png

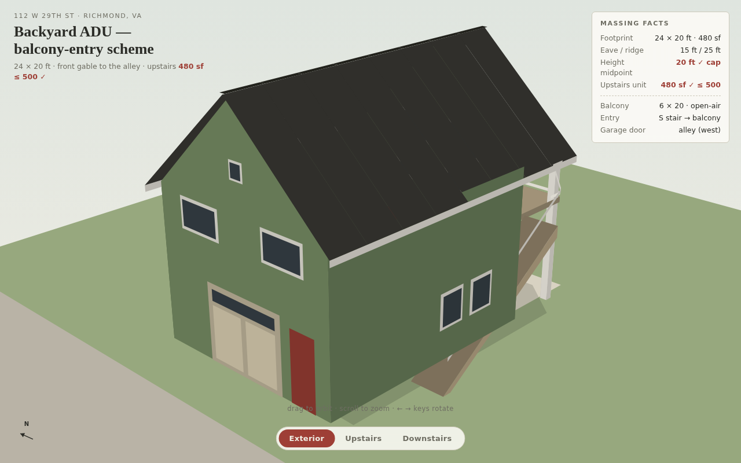
renderings/massing-3d-alley-view.png
