dataders/adu_adoration/renderings/option-e-final-alley-l-stair.png

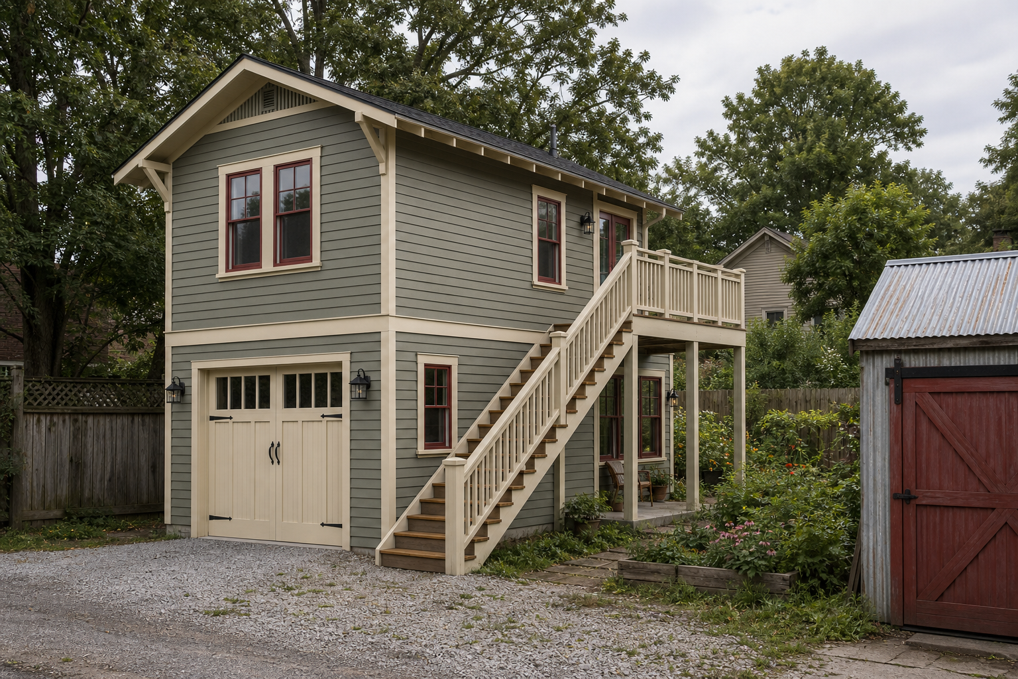
renderings/option-e-final-alley-l-stair.png
