dataders/adu_adoration/renderings/option-e-final-yard-l-stair.png

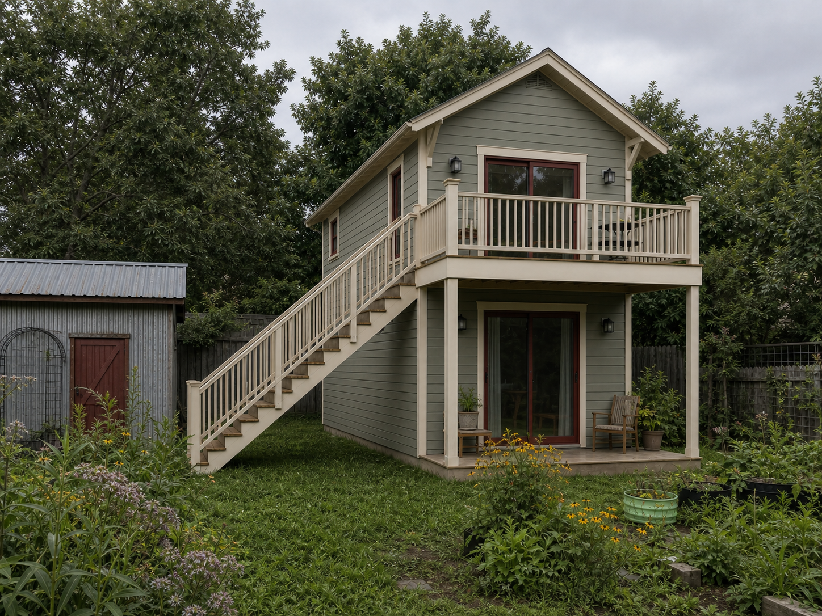
renderings/option-e-final-yard-l-stair.png
