dataders/adu_adoration/renderings/option-e-yard-east-elevation-v2.png

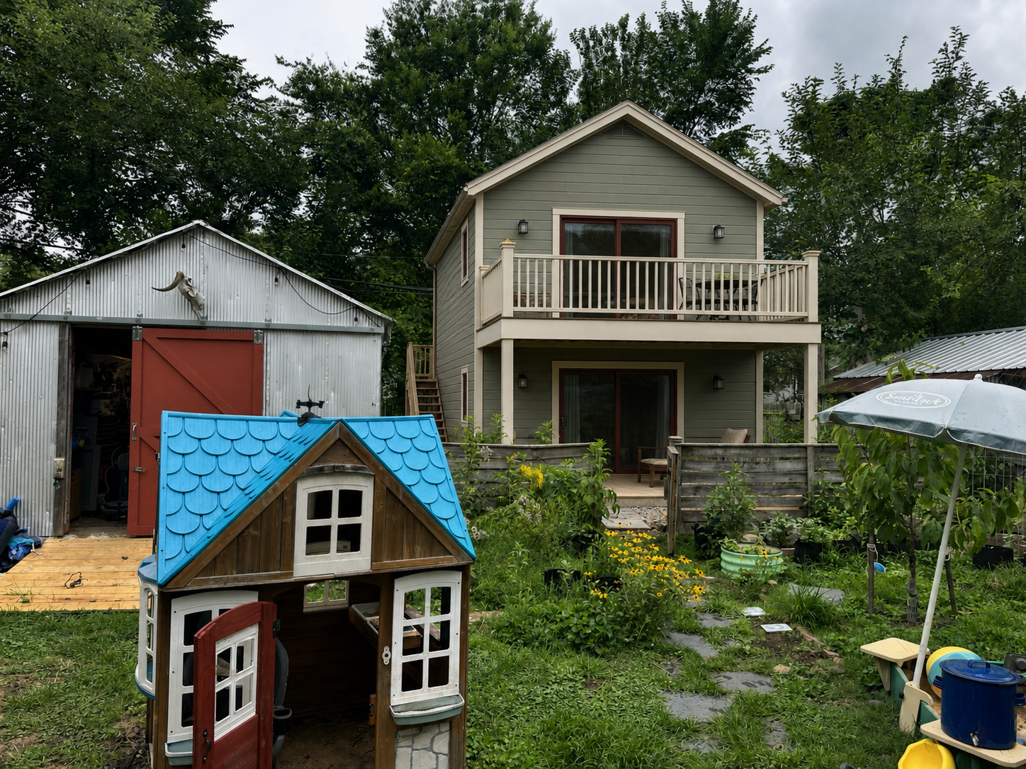
renderings/option-e-yard-east-elevation-v2.png
