dataders/adu_adoration/renderings/option-e-yard-east-elevation-v3.png

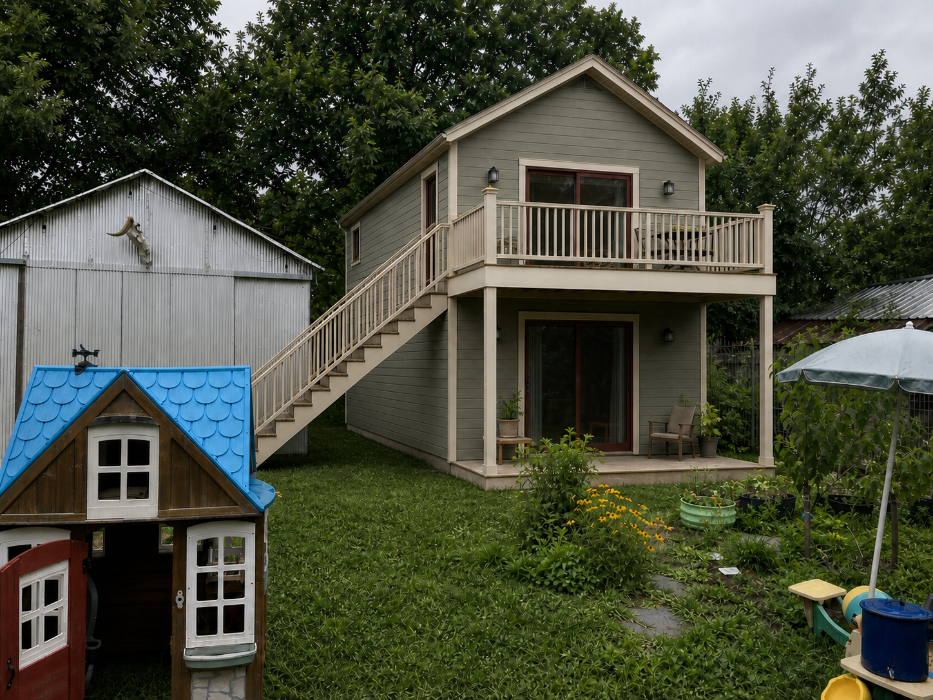
renderings/option-e-yard-east-elevation-v3.png
