dataders/adu_adoration/renderings/option-e-yard-east-elevation-v4.png

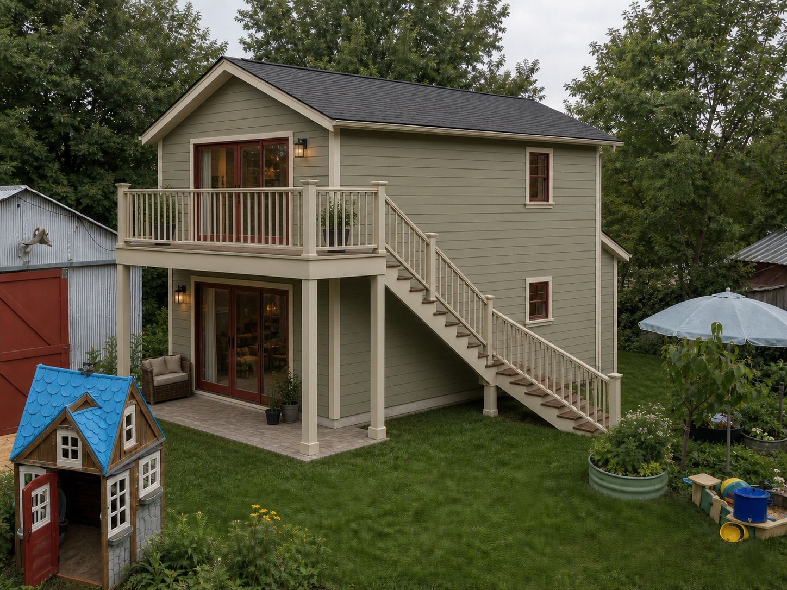
renderings/option-e-yard-east-elevation-v4.png
