dataders/adu_adoration/renderings/option-e-yard-photoreal.png

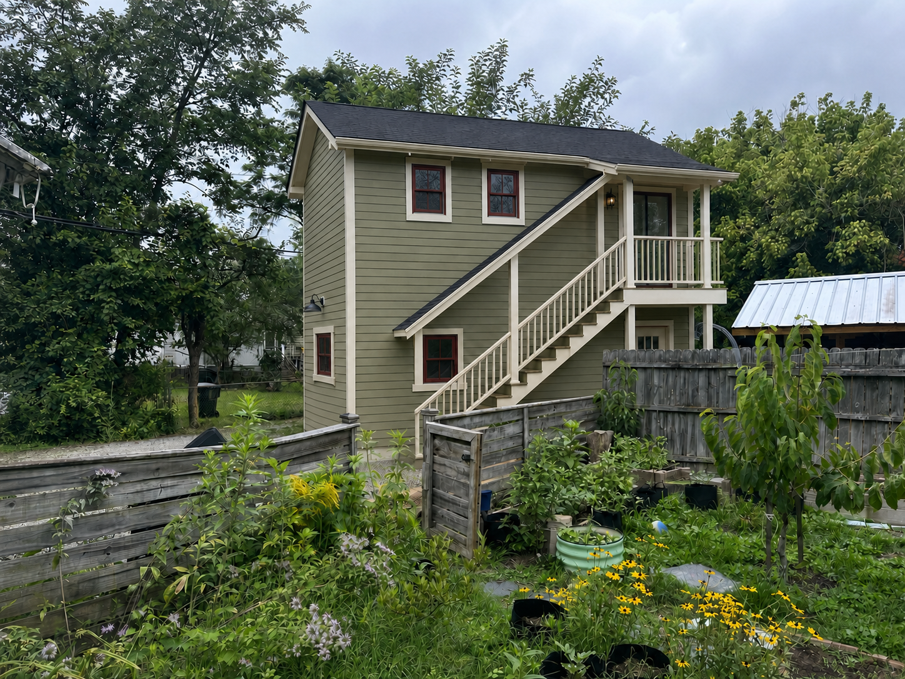
renderings/option-e-yard-photoreal.png
