dataders/adu_adoration/renderings/option-f-alley-model.png

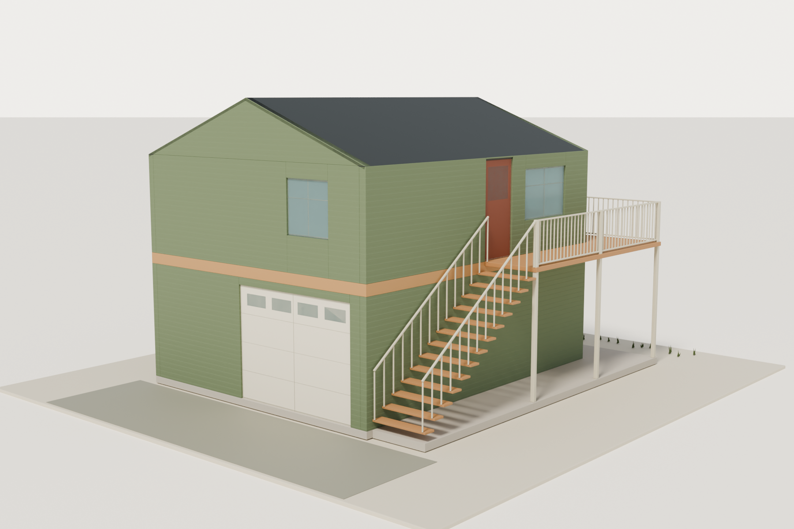
renderings/option-f-alley-model.png
