dataders/adu_adoration/renderings/option-f-alley-photoreal-v2.png

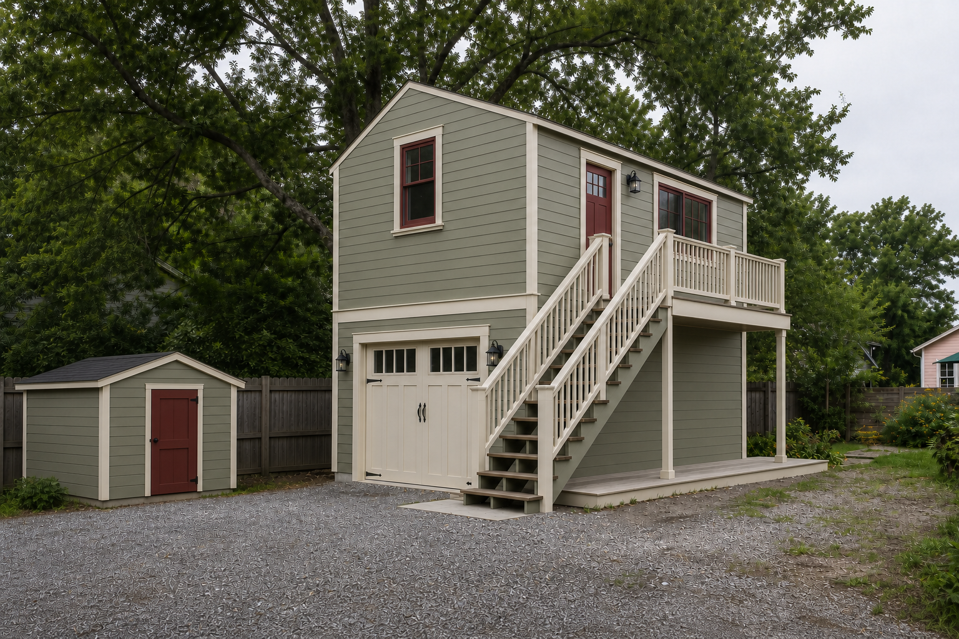
renderings/option-f-alley-photoreal-v2.png
