dataders/adu_adoration/renderings/option-f-alley-photoreal.png

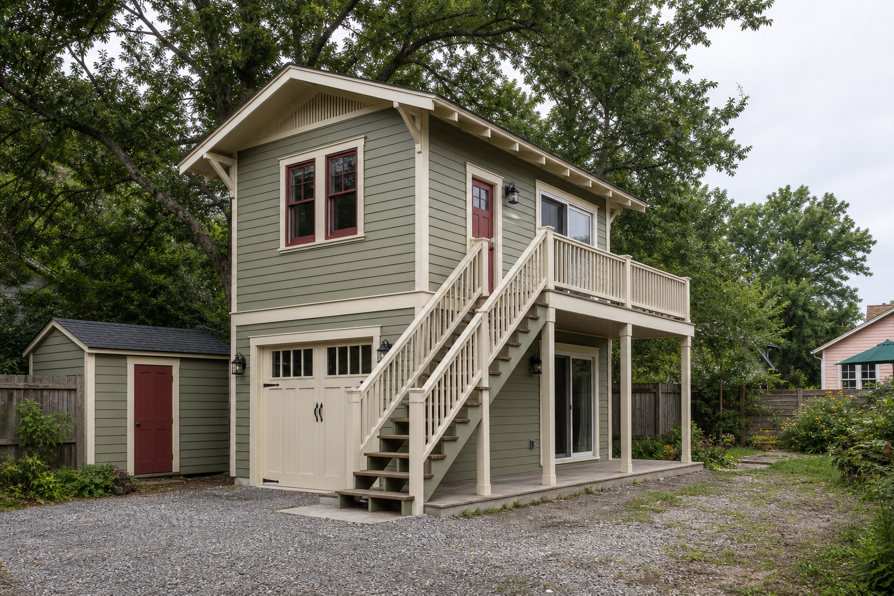
renderings/option-f-alley-photoreal.png
