dataders/adu_adoration/renderings/option-f-first-floor-interior.png

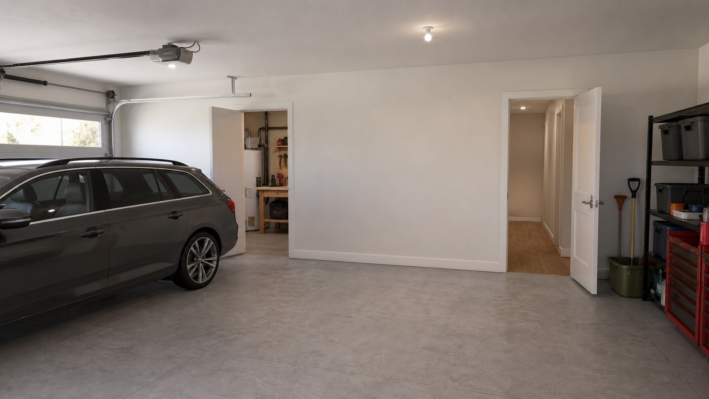
renderings/option-f-first-floor-interior.png
