dataders/adu_adoration/renderings/option-f-lower-cutaway.png

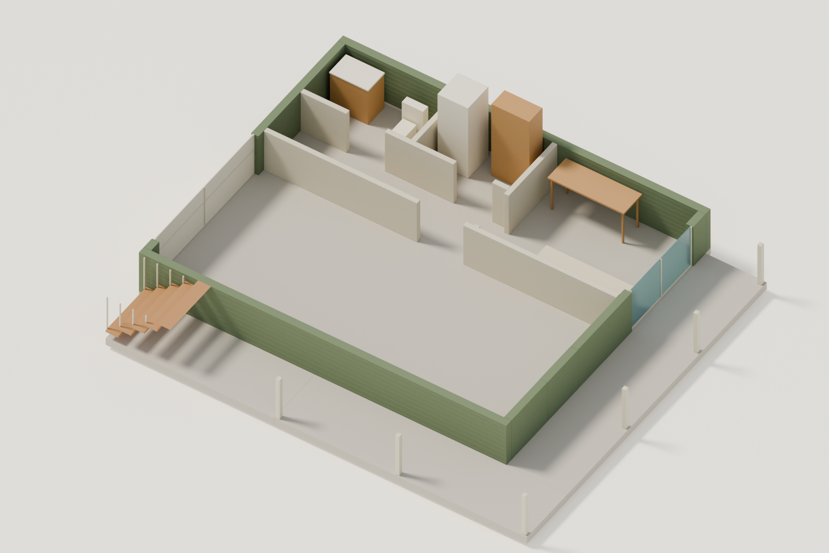
renderings/option-f-lower-cutaway.png
