dataders/adu_adoration/renderings/option-f-second-floor-interior-corrected.png

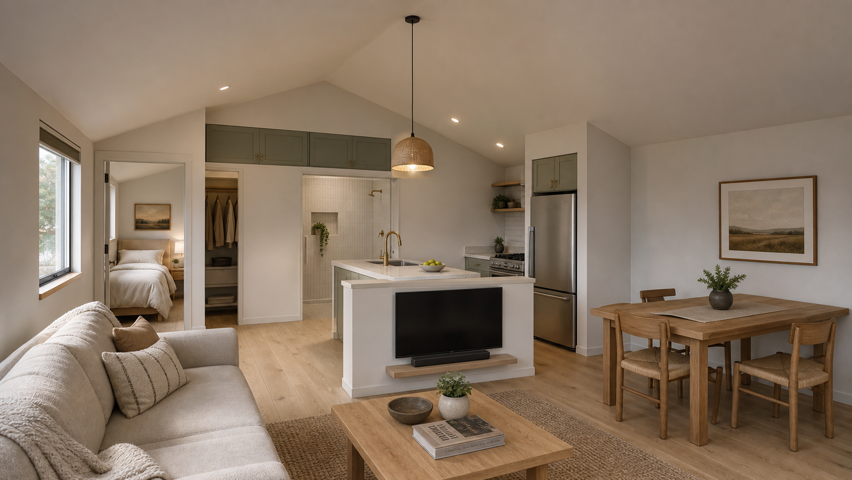
renderings/option-f-second-floor-interior-corrected.png
