dataders/adu_adoration/renderings/option-f-second-floor-interior.png

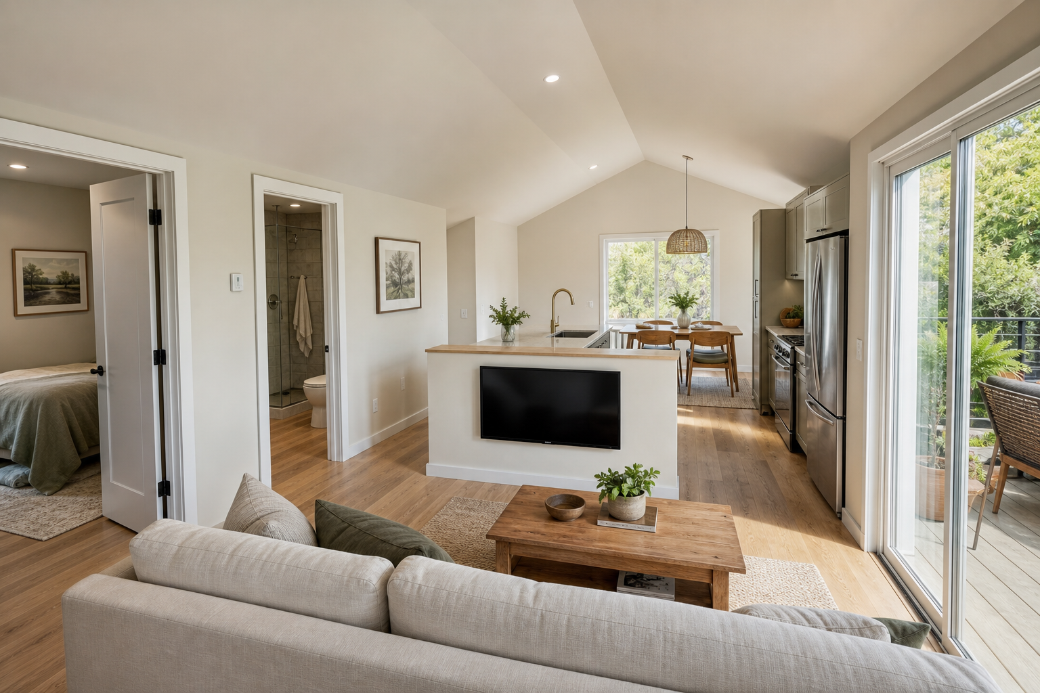
renderings/option-f-second-floor-interior.png
