dataders/adu_adoration/renderings/option-f-upper-cutaway.png

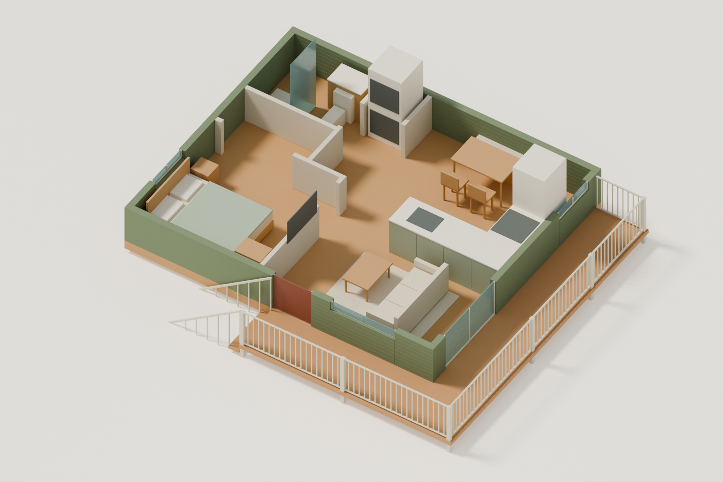
renderings/option-f-upper-cutaway.png
