dataders/adu_adoration/renderings/option-f-yard-model.png

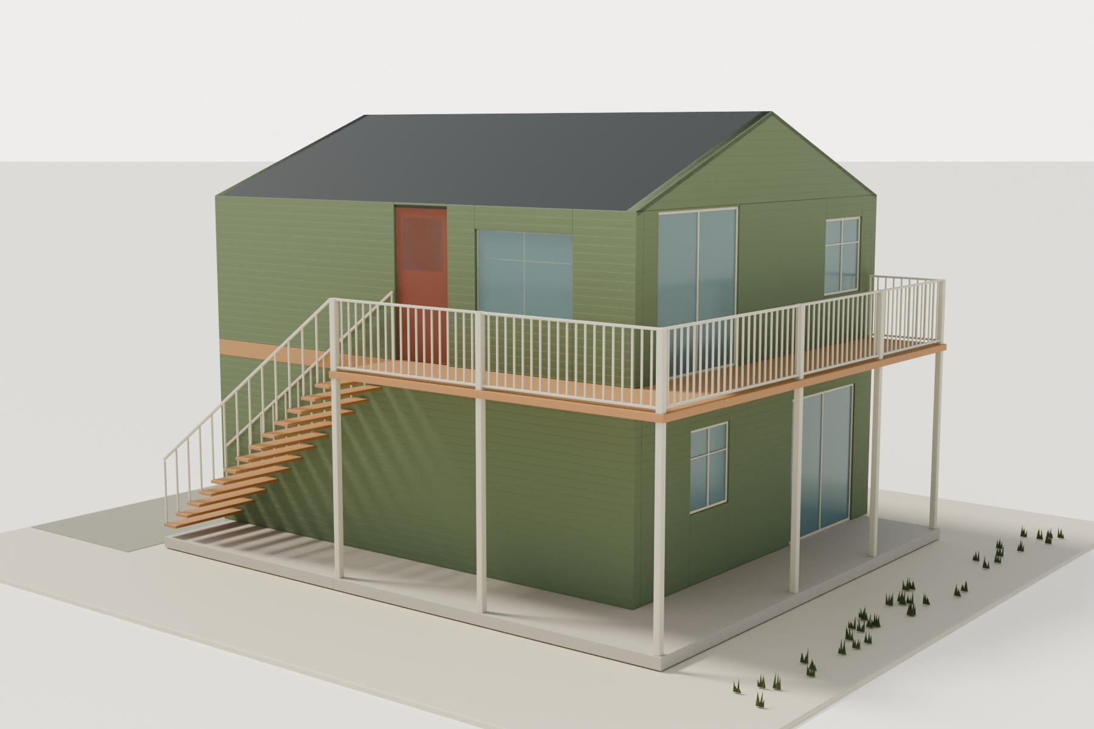
renderings/option-f-yard-model.png
