dataders/adu_adoration/renderings/option-f-yard-photoreal-v2.png

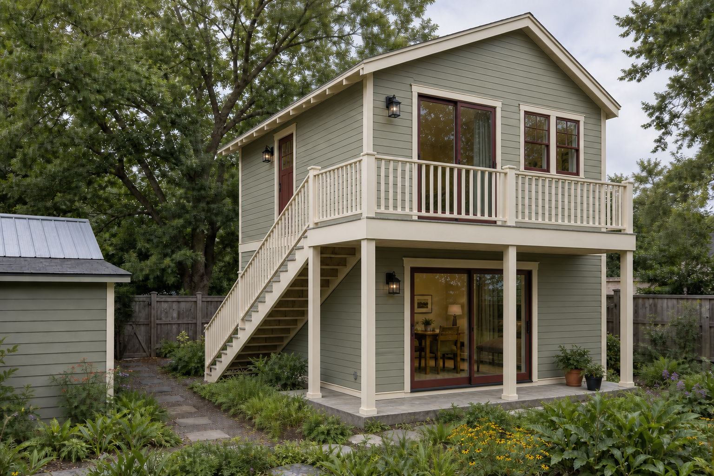
renderings/option-f-yard-photoreal-v2.png
