dataders/adu_adoration/renderings/option-g-15x30-alley-photoreal.png

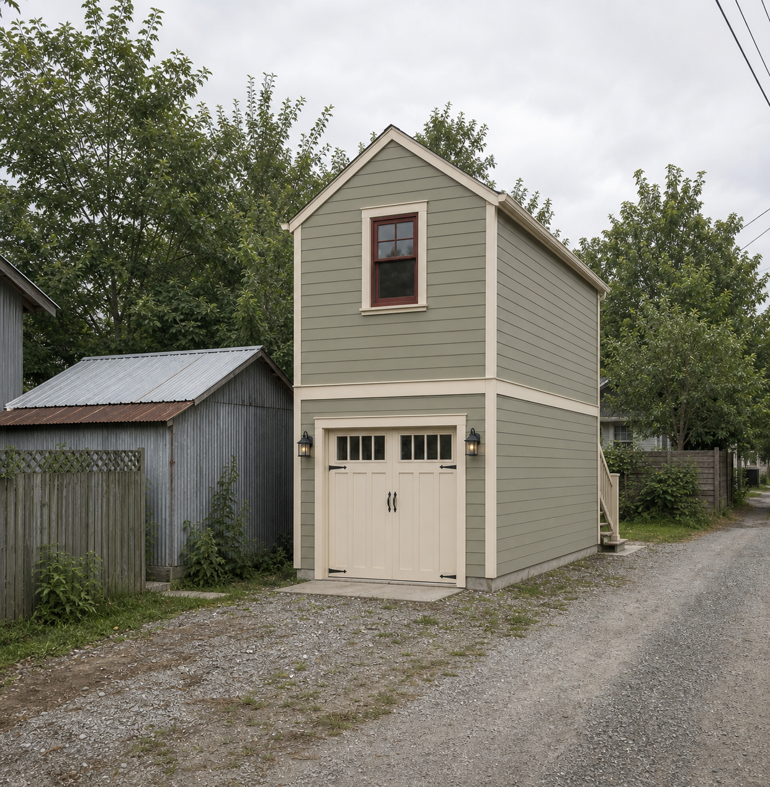
renderings/option-g-15x30-alley-photoreal.png
