dataders/adu_adoration/renderings/option-g-15x30-lower-garage-interior.png

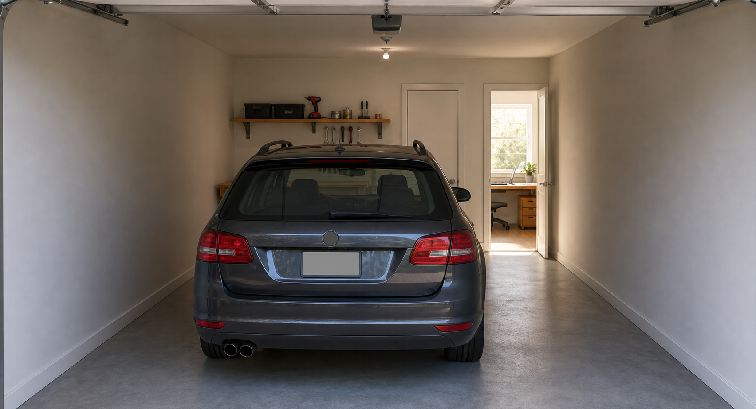
renderings/option-g-15x30-lower-garage-interior.png
