dataders/adu_adoration/renderings/option-g-15x30-upper-interior.png

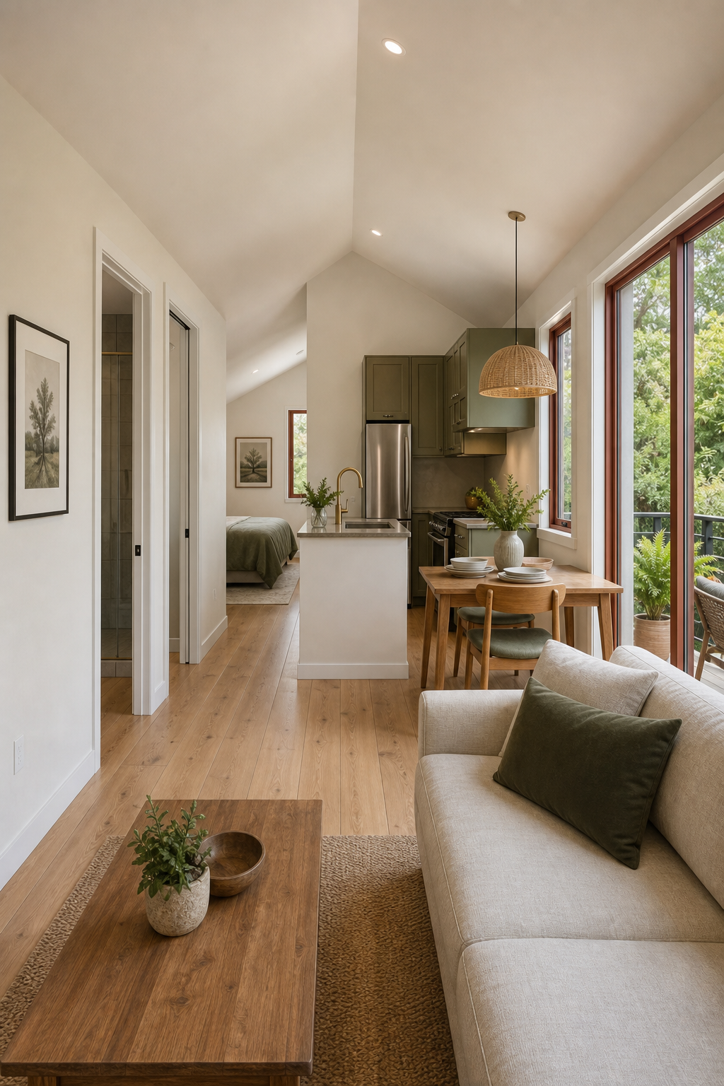
renderings/option-g-15x30-upper-interior.png
