dataders/adu_adoration/renderings/option-g-15x30-yard-photoreal.png

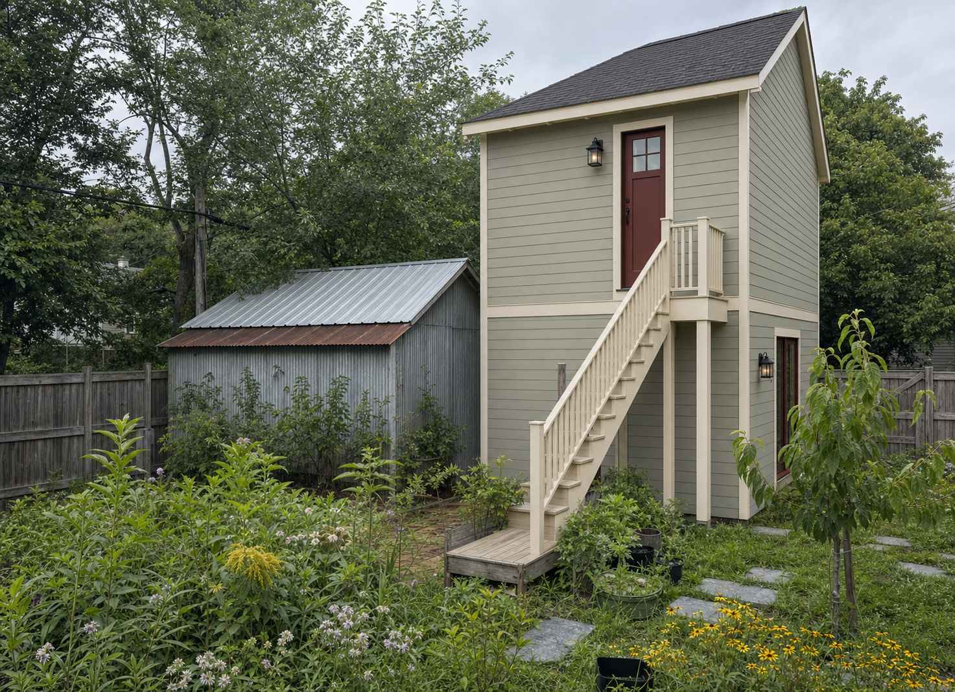
renderings/option-g-15x30-yard-photoreal.png
