dataders/adu_adoration/renderings/yard-view-craftsman.png

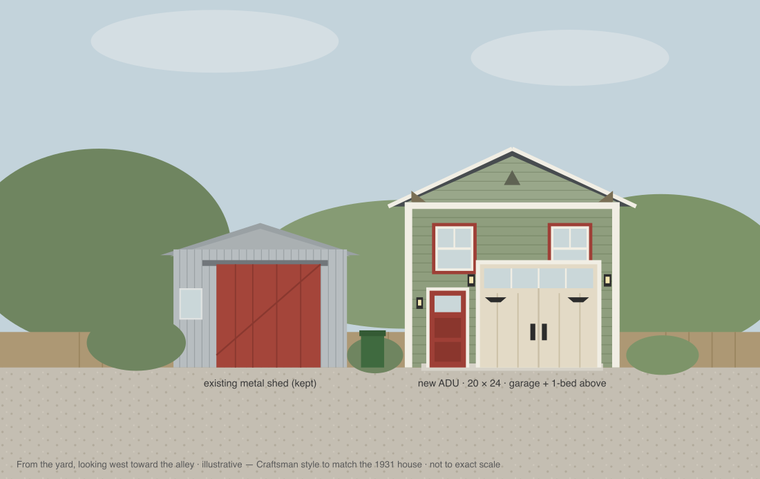
renderings/yard-view-craftsman.png
