dataders/adu_adoration/images/04-assessor-building-sketch.png

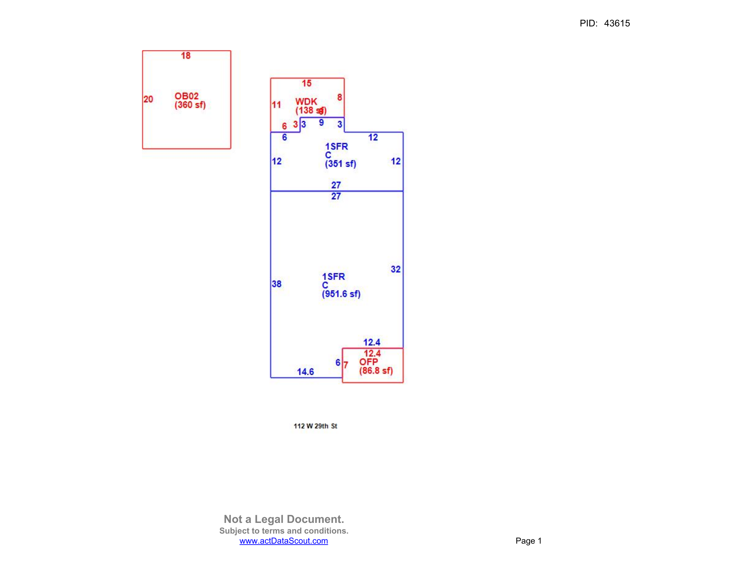
images/04-assessor-building-sketch.png
