dataders/adu_adoration/images/13-option-f-construction-set-cover.png

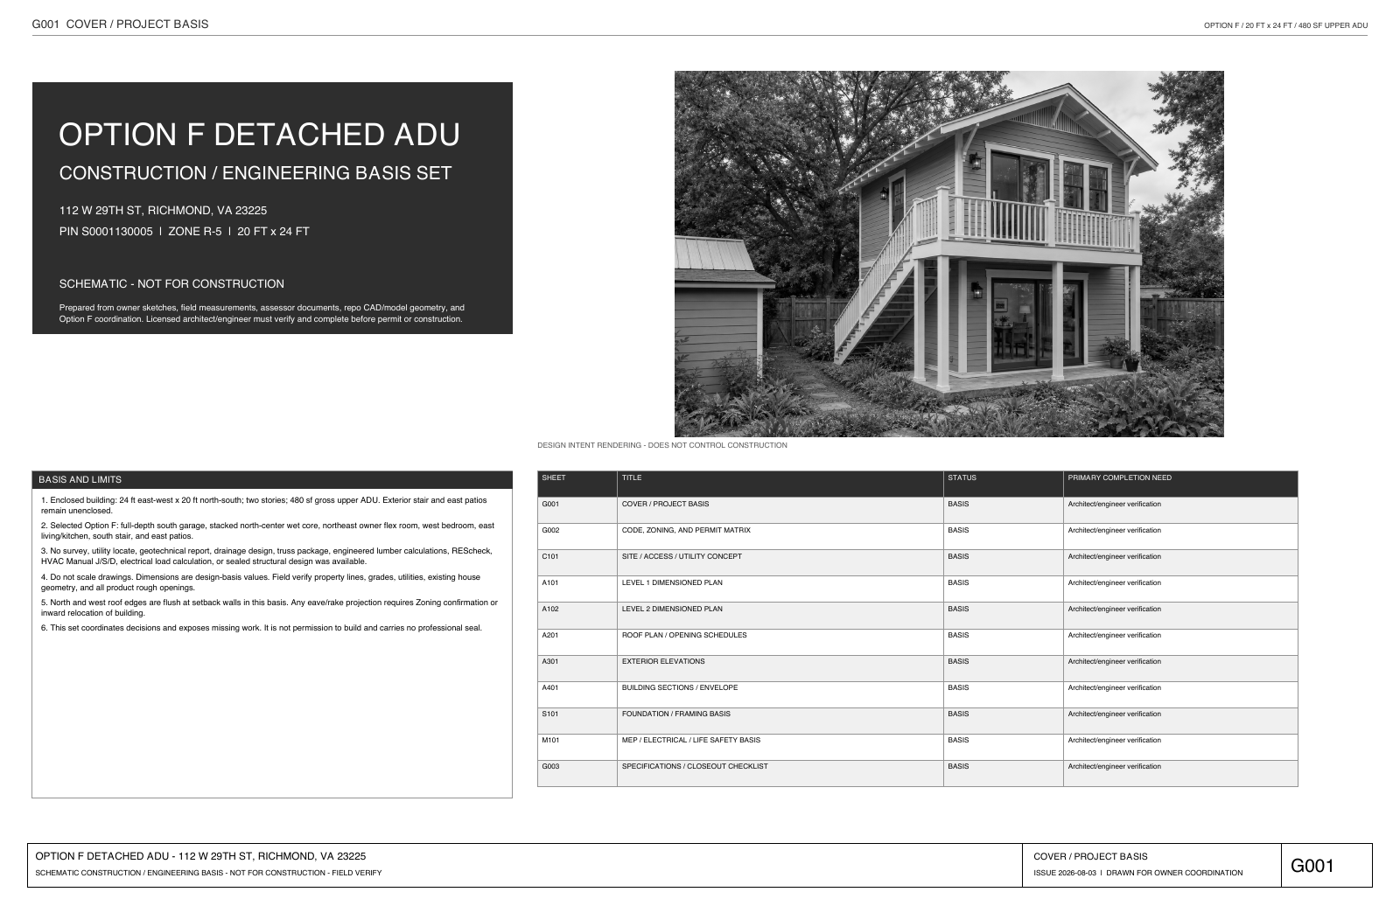
images/13-option-f-construction-set-cover.png
